nphoang1102/mqp-mech/C-term/Testing/test_top_part_Feb_18_2018_(FINISHED).SLDASM

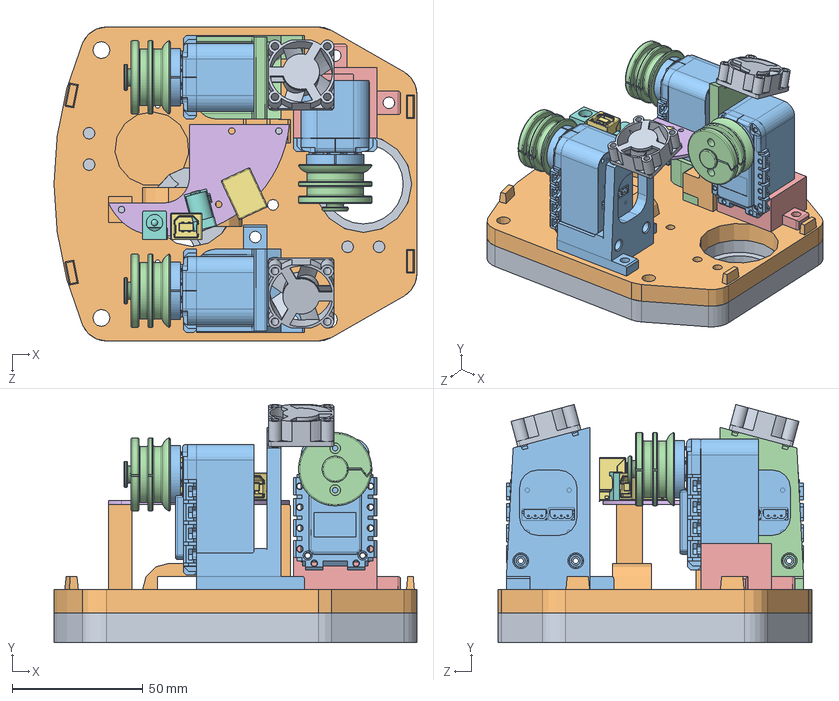
[picture p16: CAD file, 2018-03-26]
C-term/Testing/test_top_part_Feb_18_2018_(FINISHED).SLDASM
138.7 x 90.9 x 120.0 mm
base_prototype_bottom_(Feb_18_2018)
base_prototype_top_(Feb_18_2018)
mount_finger_left_(FAN_ADJUST)
mount_finger_right_(FAN_ADJUST)
mount_thumb_(MODIFIED_FOR_MOTOR)
Pcb board base
USB type b
power jack
DC Fan - 25X25X10 x 2
PCB_board_mount_standing
AX-12A (back off) x 3
pulley_spool_test x 3
