nphoang1102/mqp-mech/B-term/Prototype 1 Fixes (Not Prototype 2 Yet)/XL320_and_mount.SLDASM

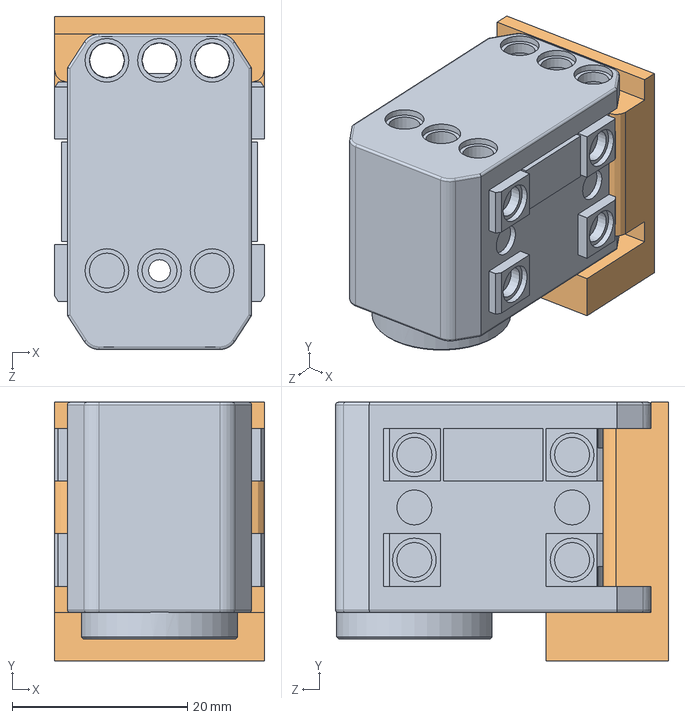
[picture p17: CAD file, 2018-03-26]
B-term/Prototype 1 Fixes (Not Prototype 2 Yet)/XL320_and_mount.SLDASM
24.0 x 29.5 x 38.0 mm
XL320
XL320_thumb_mount
