nphoang1102/mqp-mech/B-term/Prototype 1 Fixes (Not Prototype 2 Yet)/motor_pulley_thumb.SLDASM

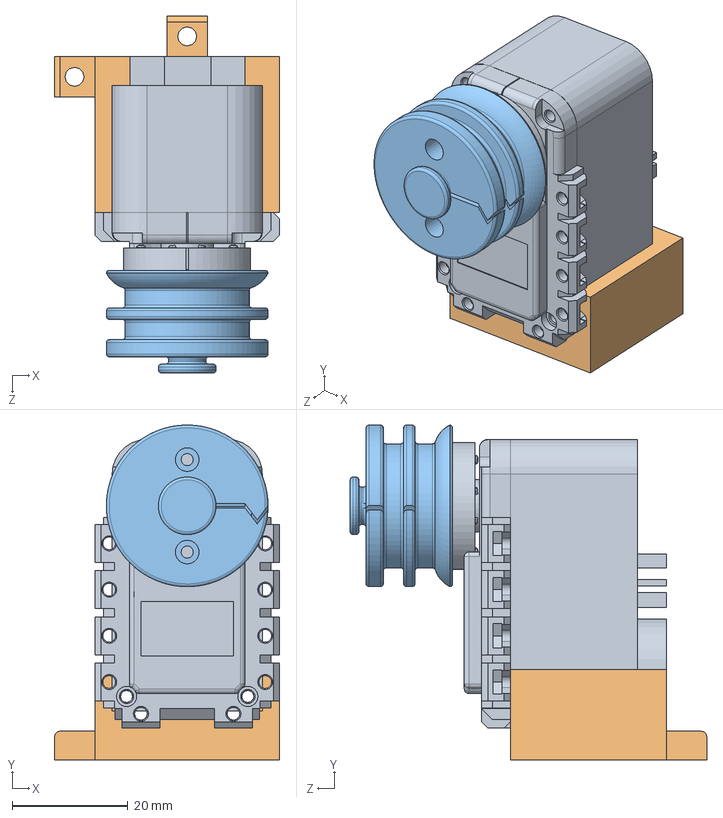
[picture p18: CAD file, 2018-03-26]
B-term/Prototype 1 Fixes (Not Prototype 2 Yet)/motor_pulley_thumb.SLDASM
39.0 x 58.0 x 61.7 mm
AX-12A (back off)
AX12_thumb_mount
pulley_spool_test
