nphoang1102/mqp-mech/B-term/Prototype 2/test_bottom_part_(FINISHED).SLDASM

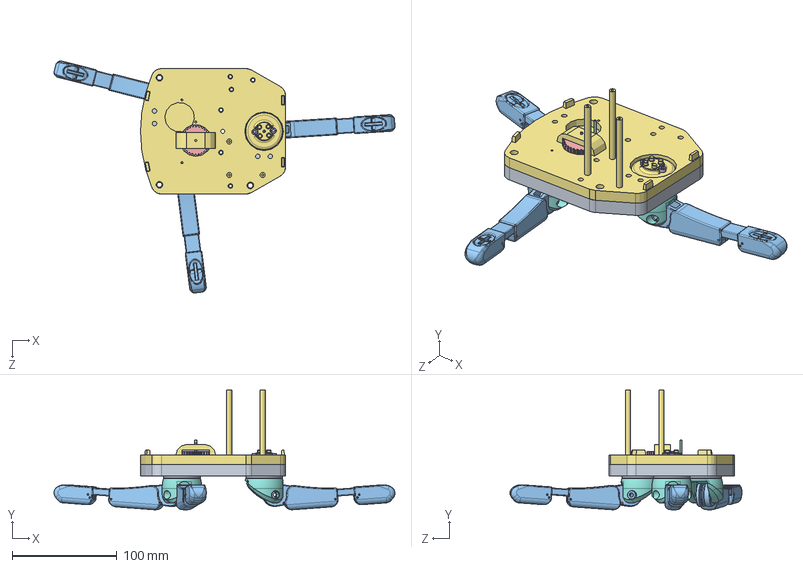
[picture p19: CAD file, 2018-03-26]
B-term/Prototype 2/test_bottom_part_(FINISHED).SLDASM
326.0 x 114.4 x 221.9 mm
base_prototype_bottom
gear_finger_left
gear_finger_right
gear_rod_(NOT_PRINT) x 2
gear_two_stage
gear_intermediate
mount_knuckle_test_modified
Knuckle mark 3 x 3
Delrin Washer x 3
M3 EZ LOCK (5.1MM HOLE) 6.5mm insert x 6
Finger x 3
M2_Washer_2.2mm_(TO_BUY)
M3_x_10mm_(TO_BUY) x 4
M3_x_22mm x 2
base_prototype_top
Hex_Nut_M4 x 6
Hex_Nut_M6 x 3
