nphoang1102/mqp-mech/A-term/motor_pulley_right.SLDASM

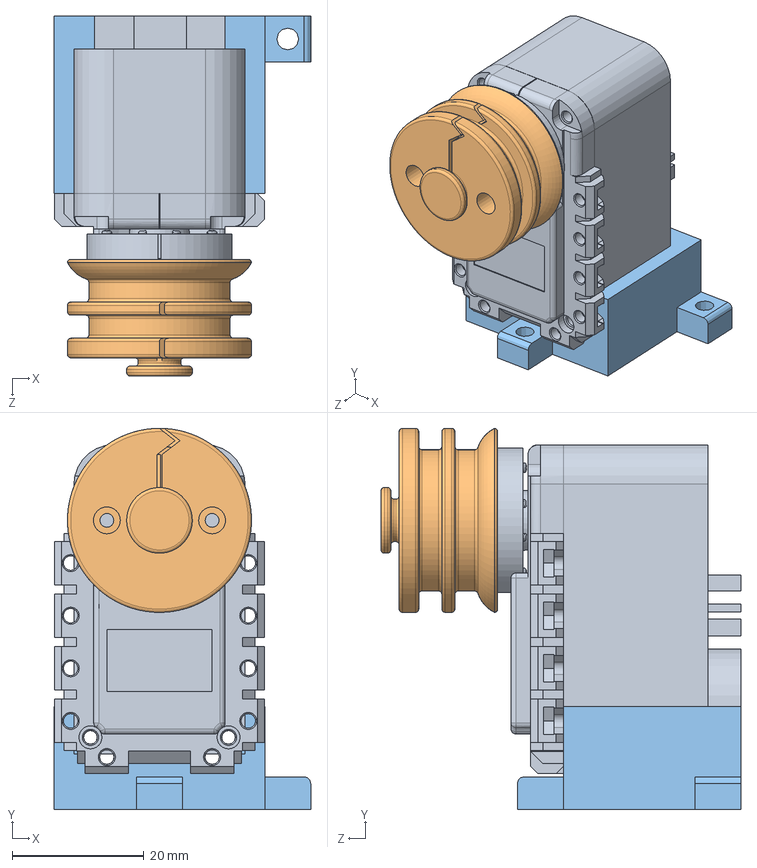
[picture p20: CAD file, 2017-10-21]
A-term/motor_pulley_right.SLDASM
39.0 x 58.0 x 54.8 mm
AX-12A (back off)
pulley_spool_test
AX12_front_mount_right
