nphoang1102/mqp-mech/B-term/Prototype 1 Fixes (Not Prototype 2 Yet)/TEST_POSITION_PROTOTYPE_2.SLDASM

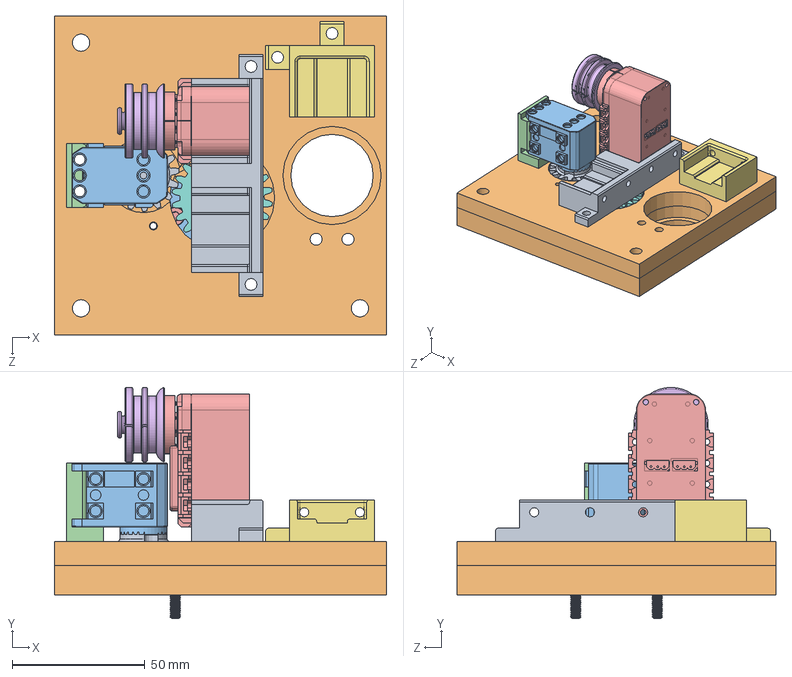
[picture p21: CAD file, 2018-03-26]
B-term/Prototype 1 Fixes (Not Prototype 2 Yet)/TEST_POSITION_PROTOTYPE_2.SLDASM
125.0 x 87.0 x 120.0 mm
two_stage_gear
drive_gear
base_prototype_test
finger_gear_left
finger_gear_right
91290A164_BLACK-OXIDE CLASS 12.9 SOCKET HEAD CAP SCREW x 2
gear_rod
