nphoang1102/mqp-mech/B-term/Prototype 2/test_top_part_with_shaft_(NOT_FINISHED).SLDASM

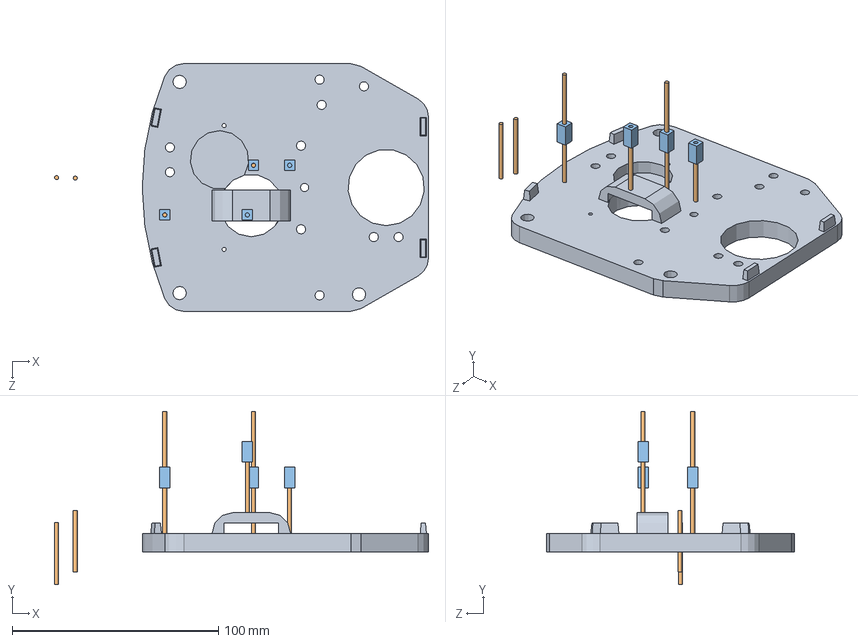
[picture p22: CAD file, 2018-03-26]
B-term/Prototype 2/test_top_part_with_shaft_(NOT_FINISHED).SLDASM
181.2 x 83.8 x 120.0 mm
base_prototype_top_(Jan_20_2018)
gear_rod_(NOT_PRINT) x 8
shaft_connector x 4
