nphoang1102/mqp-mech/B-term/Prototype 2/test_motor_pulley.SLDASM

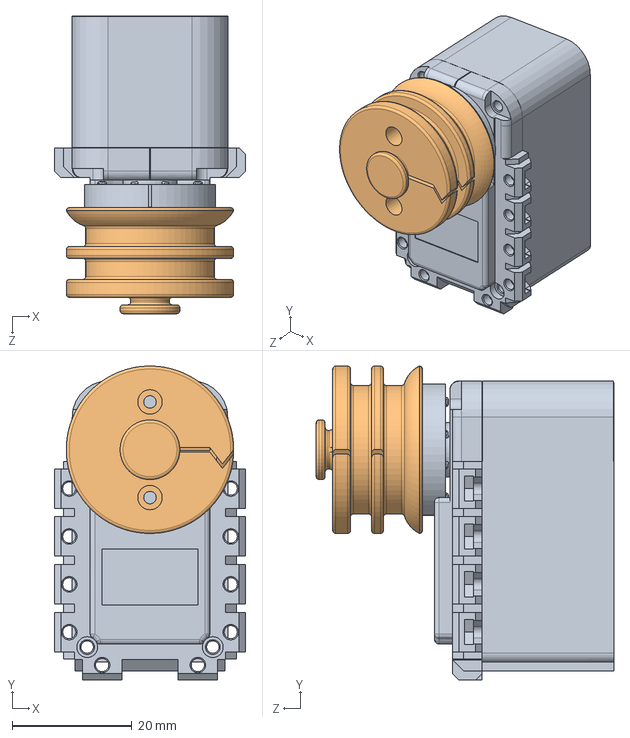
[picture p23: CAD file, 2018-03-26]
B-term/Prototype 2/test_motor_pulley.SLDASM
32.0 x 52.5 x 49.8 mm
AX-12A (back off)
pulley_spool_test
