nphoang1102/mqp-mech/A-term/motor_pulley_left.SLDASM

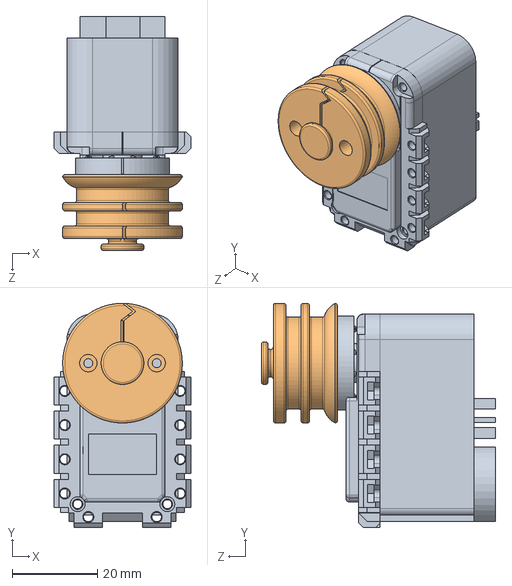
[picture p24: CAD file, 2017-10-21]
A-term/motor_pulley_left.SLDASM
32.0 x 52.5 x 54.8 mm
AX-12A (back off)
pulley_spool_test
