nphoang1102/mqp-mech/A-term/gears_train.SLDASM

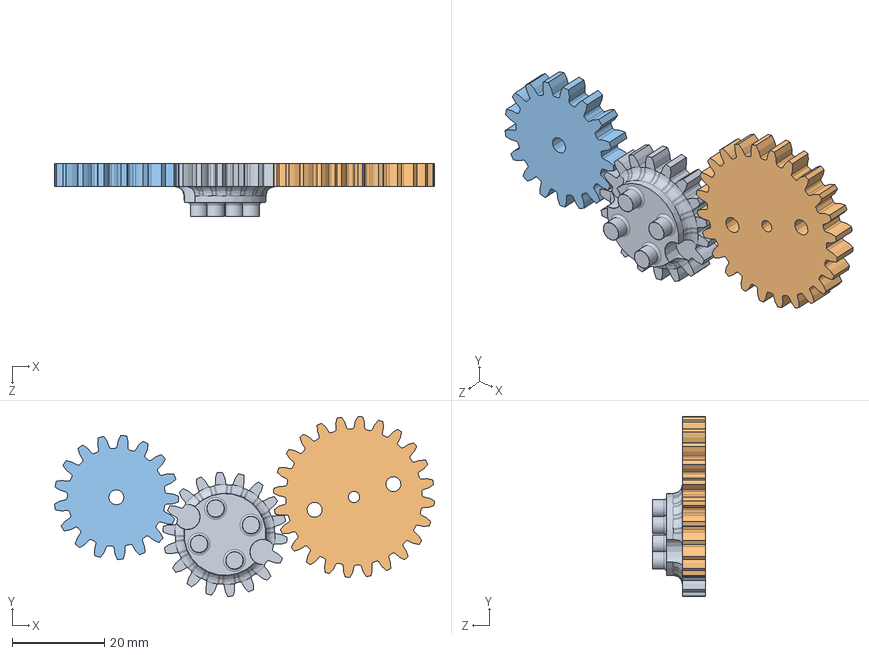
[picture p26: CAD file, 2017-10-08]
A-term/gears_train.SLDASM
82.5 x 39.1 x 11.5 mm
drive_gear
finger_gear
intermediate_gear
