nphoang1102/mqp-mech/A-term/positioning_motors_test.SLDASM

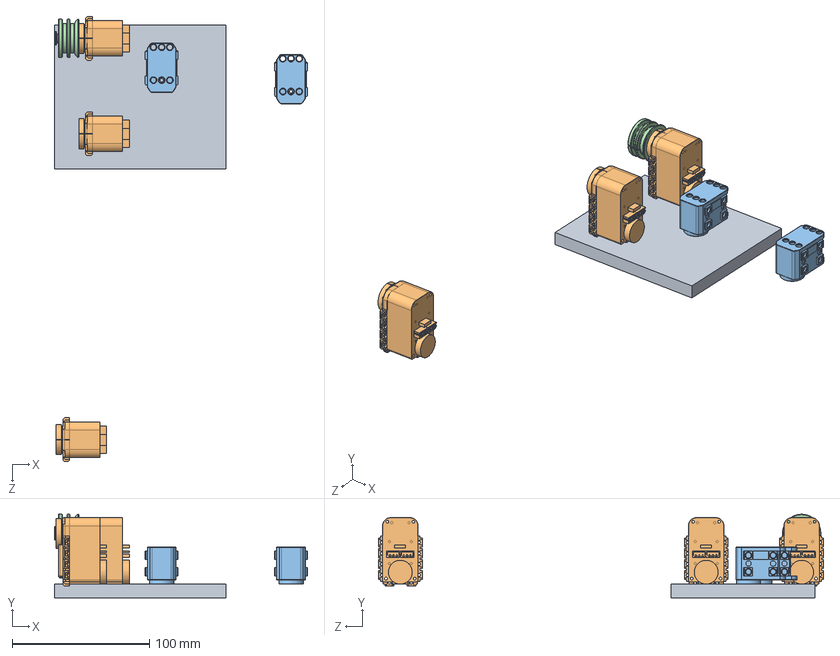
[picture p27: CAD file, 2017-10-04]
A-term/positioning_motors_test.SLDASM
184.6 x 61.0 x 324.8 mm
base_prototype_test
AX-12A (back off) x 3
XL320 x 2
pulley_spool_test
