nphoang1102/mqp-mech/B-term/Prototype 1 Fixes (Not Prototype 2 Yet)/finger_gear_right.SLDPRT

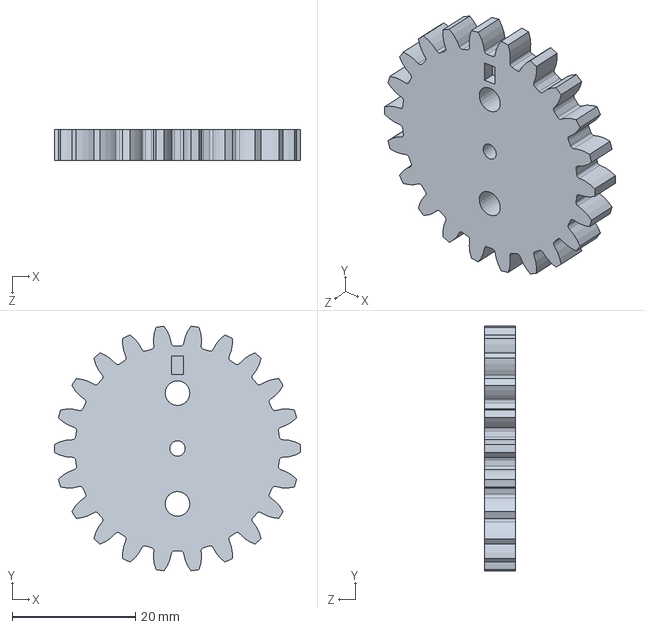
[picture p28: CAD file, 2018-03-26]
B-term/Prototype 1 Fixes (Not Prototype 2 Yet)/finger_gear_right.SLDPRT
40.0 x 39.8 x 5.00 mm
