nphoang1102/mqp-mech/B-term/Prototype 2/mount_board_(NOT_FINISHED).SLDPRT

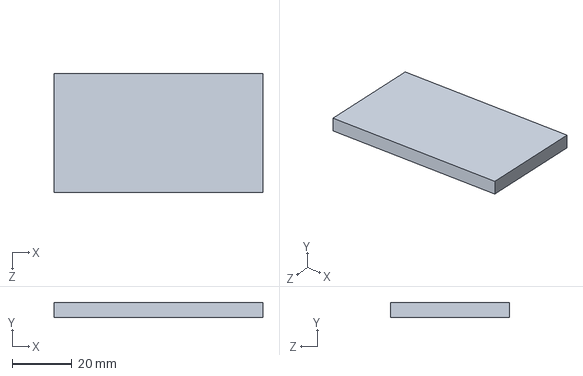
[picture p29: CAD file, 2018-03-26]
B-term/Prototype 2/mount_board_(NOT_FINISHED).SLDPRT
70.0 x 5.00 x 40.0 mm
