nphoang1102/mqp-mech/B-term/Prototype 2/STL/base_prototype_bottom_(Jan_10_2018).STL

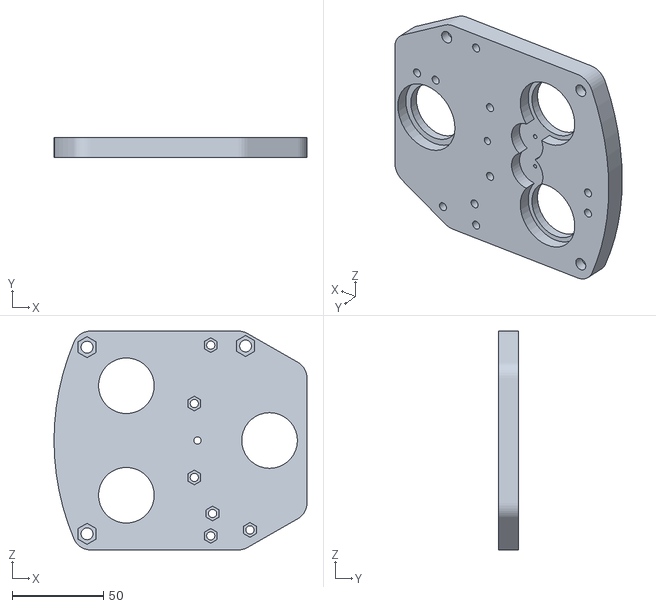
[picture p30: CAD file, 2018-03-26]
B-term/Prototype 2/STL/base_prototype_bottom_(Jan_10_2018).STL
138.7 x 11.2 x 120.0
