nphoang1102/mqp-mech/B-term/ReflexOne Finger/Knuckle mark 3.SLDPRT

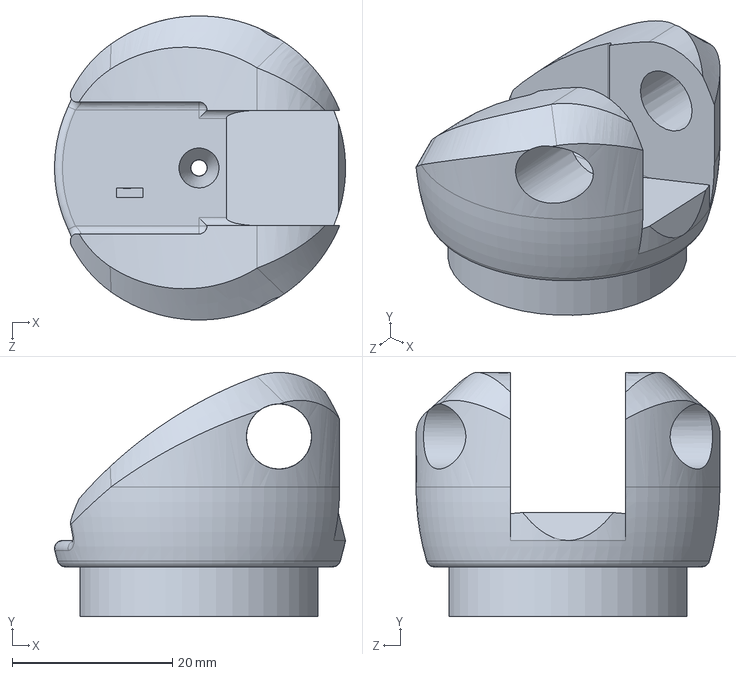
[picture p31: CAD file, 2018-03-26]
B-term/ReflexOne Finger/Knuckle mark 3.SLDPRT
36.4 x 30.5 x 38.0 mm
