nphoang1102/mqp-mech/C-term/Modified Parts/mount_finger_left.SLDPRT

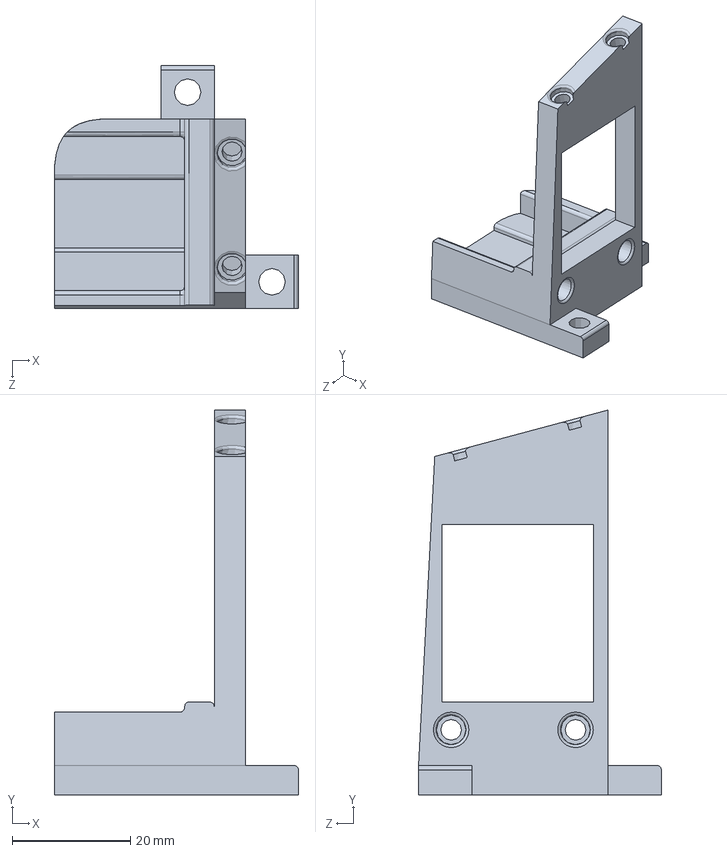
[picture p32: CAD file, 2018-03-26]
C-term/Modified Parts/mount_finger_left.SLDPRT
41.2 x 65.0 x 41.0 mm
