nphoang1102/mqp-mech/C-term/Mounting Parts/camera_adapter_base_modified.SLDPRT

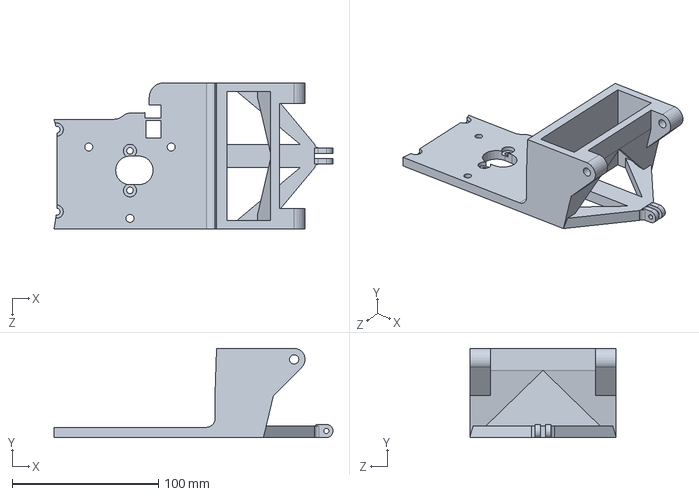
[picture p33: CAD file, 2018-03-26]
C-term/Mounting Parts/camera_adapter_base_modified.SLDPRT
190.5 x 60.9 x 100.0 mm
