nphoang1102/mqp-mech/C-term/STL toPrint/Feb_11_2018/base_prototype_top_(Feb_9_2018).STL

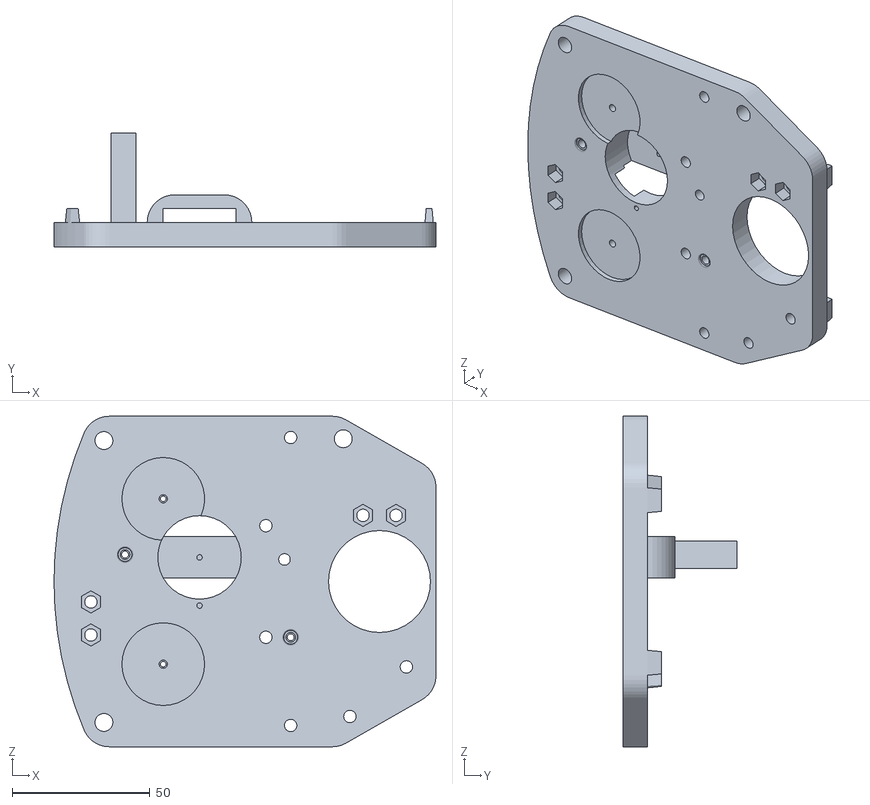
[picture p34: CAD file, 2018-03-26]
C-term/STL toPrint/Feb_11_2018/base_prototype_top_(Feb_9_2018).STL
138.7 x 41.5 x 120.0
