nphoang1102/mqp-mech/C-term/STL toPrint/Feb_13_2018/glove_housing_top.STL

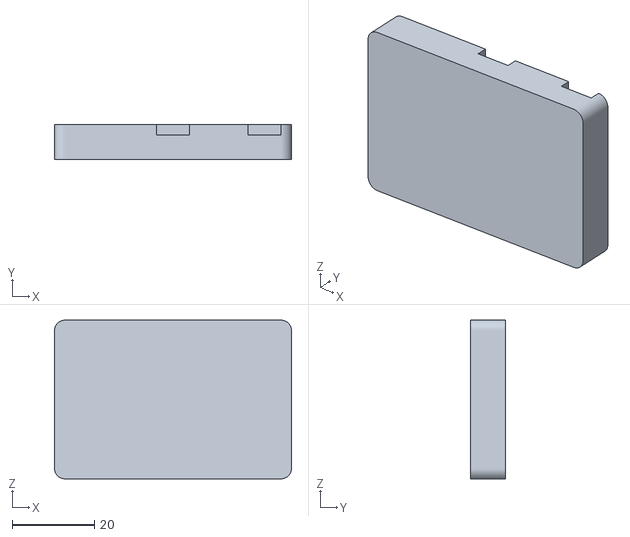
[picture p35: CAD file, 2018-03-26]
C-term/STL toPrint/Feb_13_2018/glove_housing_top.STL
57.5 x 8.50 x 38.5
