nphoang1102/mqp-mech/C-term/STL toPrint/Feb_25_2018/housing.STL

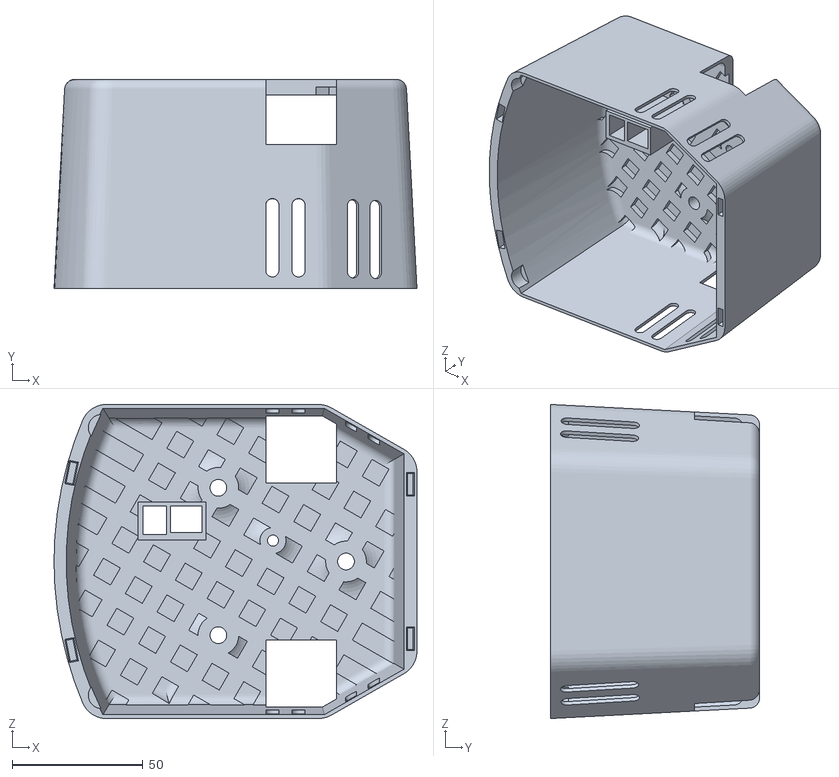
[picture p37: CAD file, 2018-03-26]
C-term/STL toPrint/Feb_25_2018/housing.STL
138.7 x 80.0 x 120.0
