nphoang1102/mqp-mech/C-term/STL toPrint/Feb_28_2018_RapidPrototyping/gear_two_stage.STL

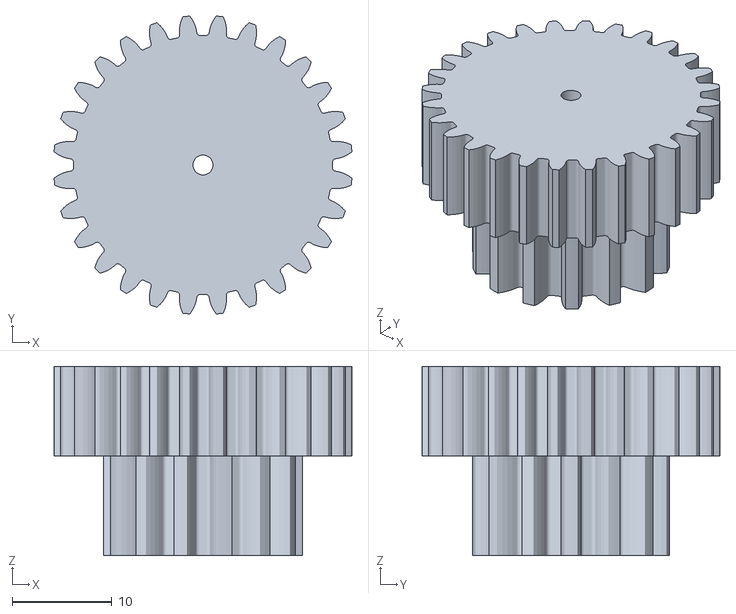
[picture p39: CAD file, 2018-03-26]
C-term/STL toPrint/Feb_28_2018_RapidPrototyping/gear_two_stage.STL
29.9 x 29.9 x 19.0
