nphoang1102/mqp-mech/C-term/STL toPrint/March_22_2018/mount_finger_right_(FAN_ADJUST).STL

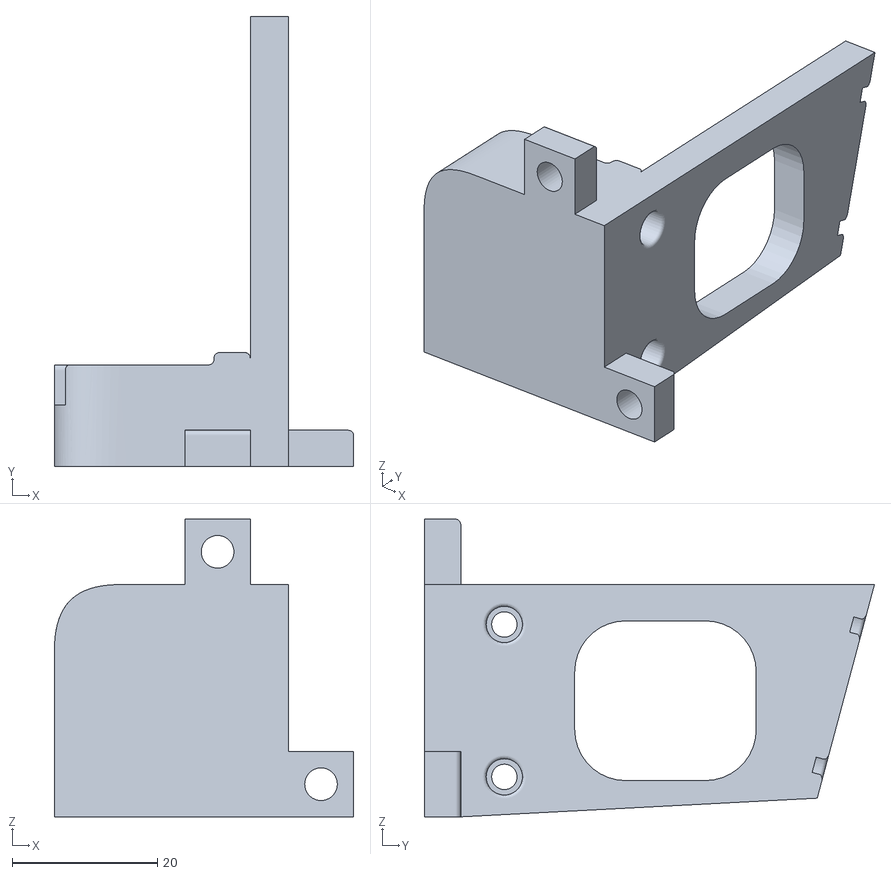
[picture p40: CAD file, 2018-03-26]
C-term/STL toPrint/March_22_2018/mount_finger_right_(FAN_ADJUST).STL
41.2 x 62.0 x 41.0
