nphoang1102/mqp-mech/A-term/base_prototype_test.SLDPRT

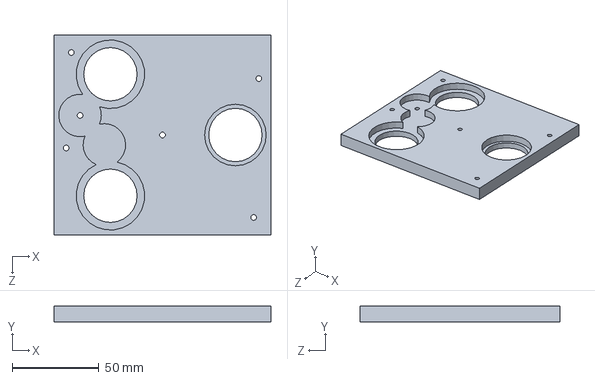
[picture p41: CAD file, 2017-10-24]
A-term/base_prototype_test.SLDPRT
125.0 x 9.22 x 115.0 mm
