nphoang1102/mqp-mech/B-term/Prototype 1 Fixes (Not Prototype 2 Yet)/gear_rod.SLDPRT

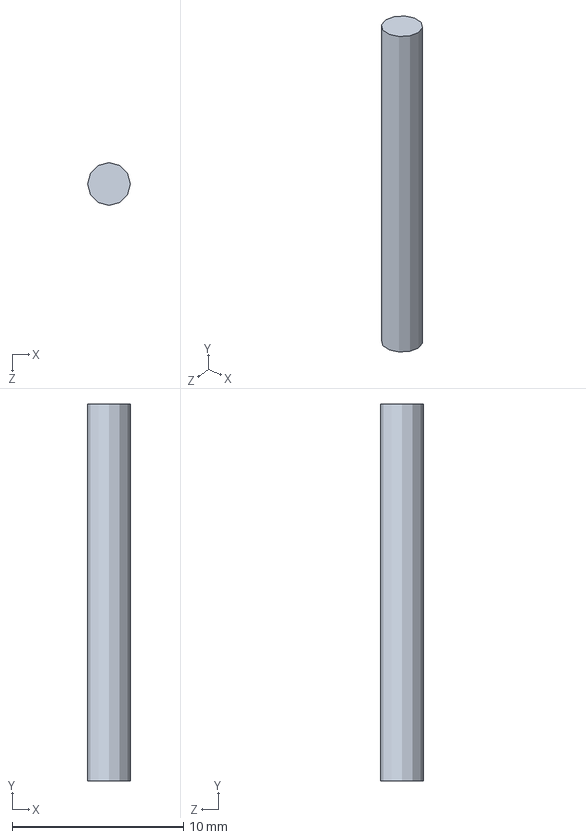
[picture p42: CAD file, 2018-03-26]
B-term/Prototype 1 Fixes (Not Prototype 2 Yet)/gear_rod.SLDPRT
2.50 x 22.0 x 2.50 mm
