nphoang1102/mqp-mech/B-term/Prototype 2/pulley_spool_test.SLDPRT

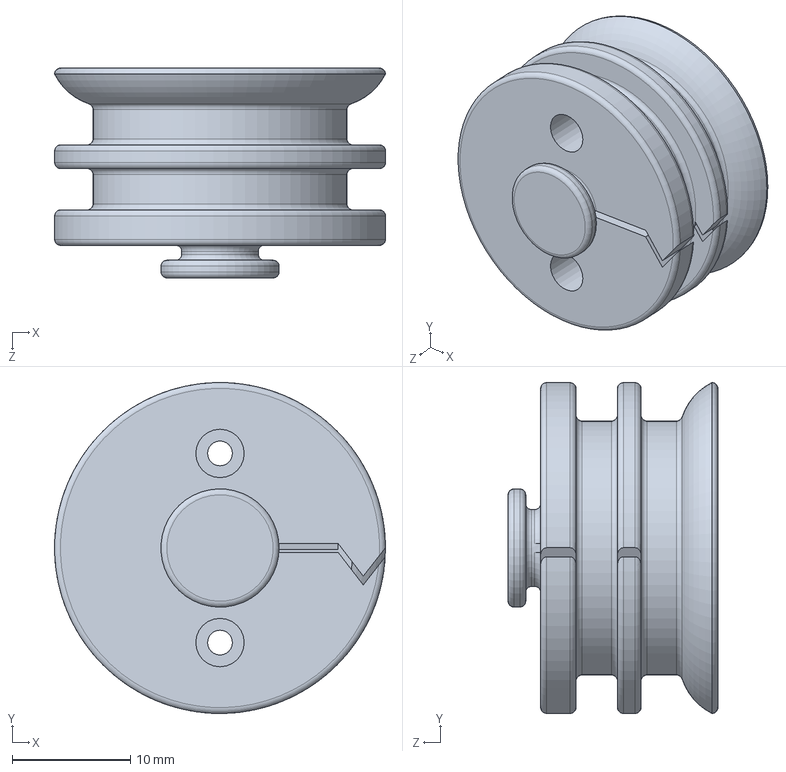
[picture p43: CAD file, 2018-03-26]
B-term/Prototype 2/pulley_spool_test.SLDPRT
28.0 x 28.0 x 17.8 mm
