nphoang1102/mqp-mech/B-term/Prototype 2/STL/housing.STL

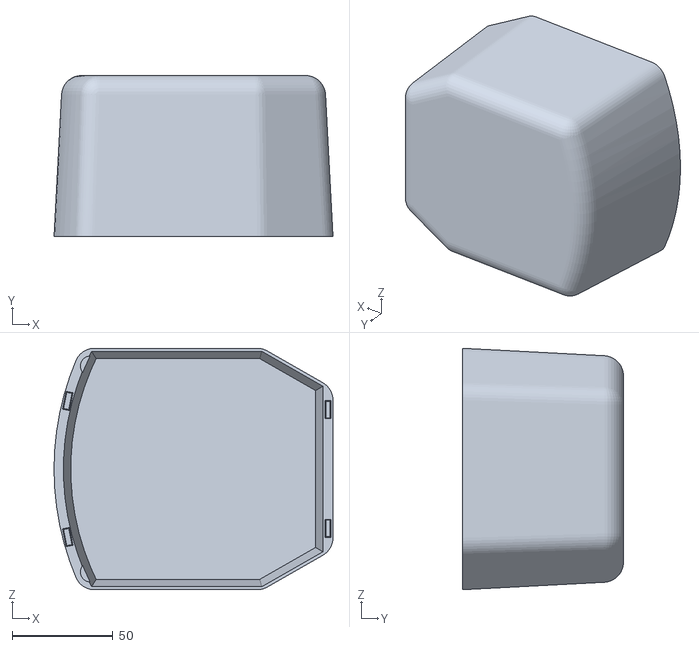
[picture p44: CAD file, 2018-03-26]
B-term/Prototype 2/STL/housing.STL
138.7 x 80.0 x 120.0
