nphoang1102/mqp-mech/C-term/Modified Parts/housing_(FINISHED).SLDPRT

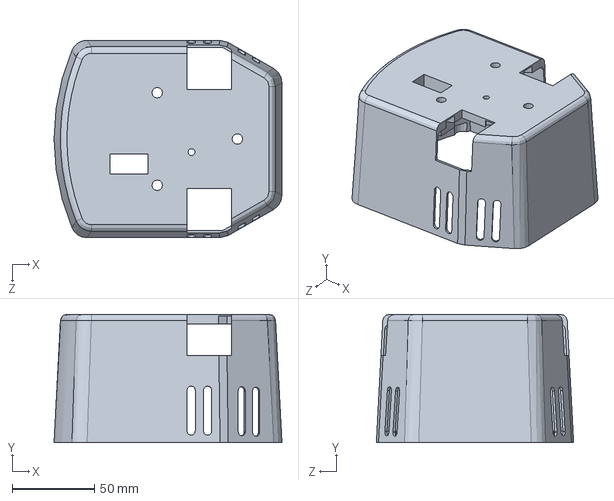
[picture p45: CAD file, 2018-03-26]
C-term/Modified Parts/housing_(FINISHED).SLDPRT
138.7 x 78.0 x 120.0 mm
