nphoang1102/mqp-mech/C-term/Mounting Parts/mounting_house/Camera Mount/ReflexHand_Camera_Adaptor_v2.SLDPRT

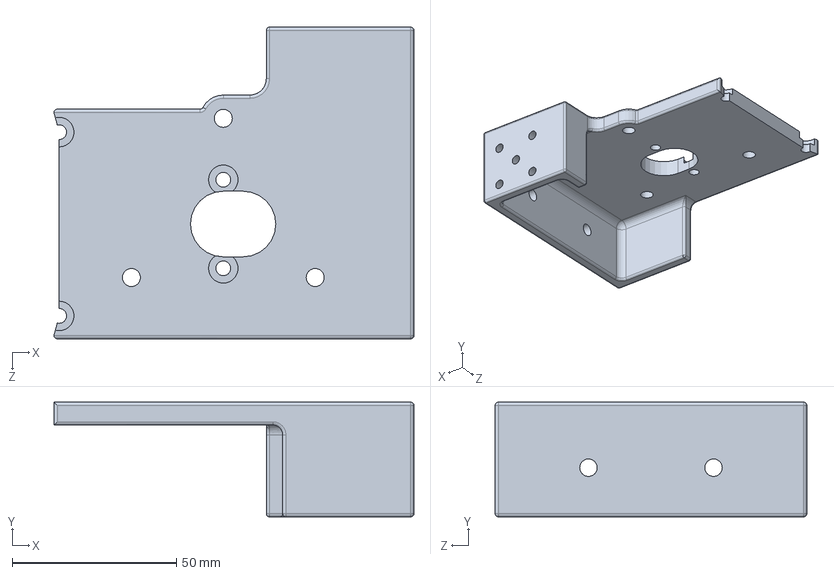
[picture p46: CAD file, 2018-03-26]
C-term/Mounting Parts/mounting_house/Camera Mount/ReflexHand_Camera_Adaptor_v2.SLDPRT
109.7 x 35.0 x 95.0 mm
