nphoang1102/mqp-mech/C-term/Mounting Parts/test_shape_fan_mount.SLDPRT

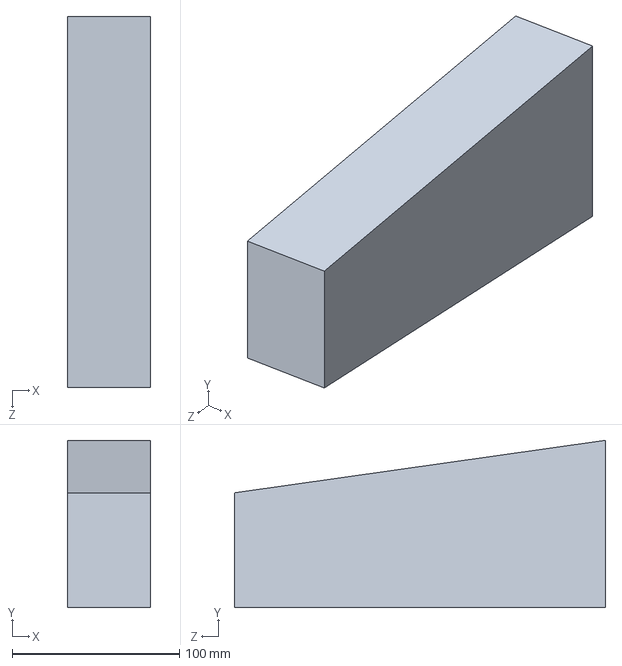
[picture p47: CAD file, 2018-03-26]
C-term/Mounting Parts/test_shape_fan_mount.SLDPRT
49.6 x 100.0 x 221.7 mm
