nphoang1102/mqp-mech/C-term/PCB Mount/USB type b.SLDPRT

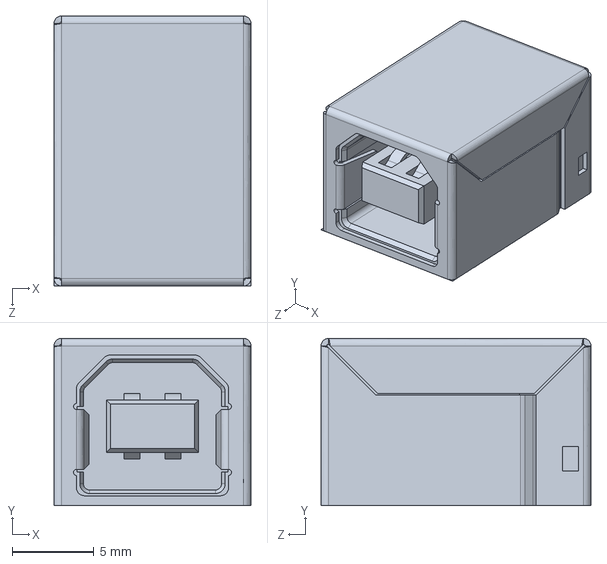
[picture p48: CAD file, 2018-03-26]
C-term/PCB Mount/USB type b.SLDPRT
12.0 x 10.2 x 16.5 mm
