nphoang1102/mqp-mech/C-term/STL toPrint/Feb_11_2018/mount_thumb.STL

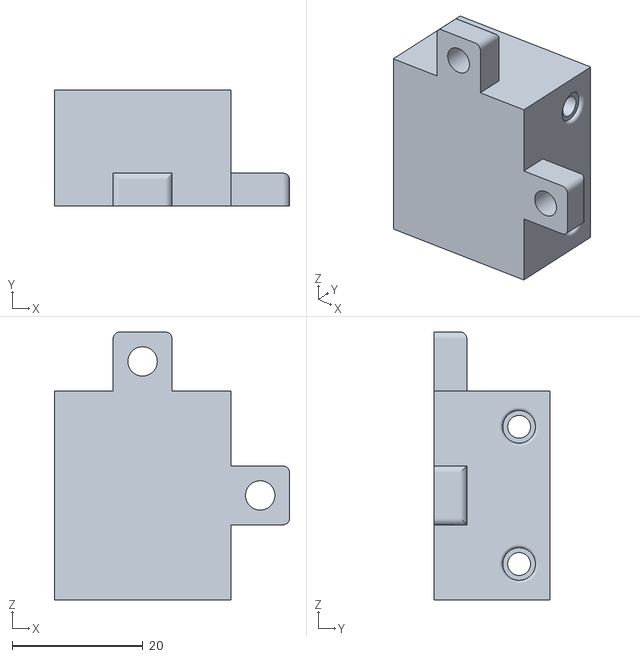
[picture p49: CAD file, 2018-03-26]
C-term/STL toPrint/Feb_11_2018/mount_thumb.STL
36.0 x 17.7 x 41.0
