nphoang1102/mqp-mech/C-term/STL toPrint/Feb_13_2018/glove_housing_bottom.STL

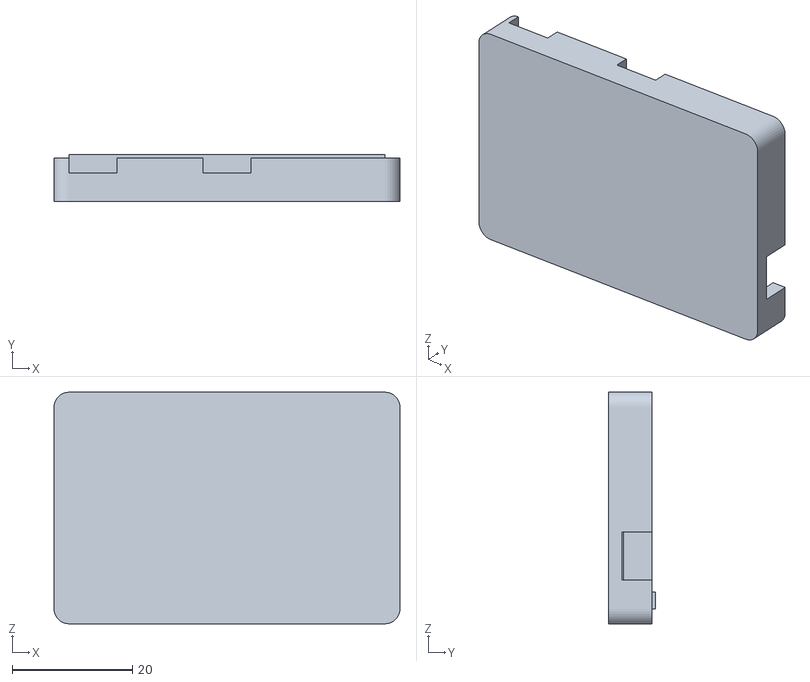
[picture p50: CAD file, 2018-03-26]
C-term/STL toPrint/Feb_13_2018/glove_housing_bottom.STL
57.5 x 7.85 x 38.5
