nphoang1102/mqp-mech/C-term/STL toPrint/Feb_28_2018_RapidPrototyping/mount_XL320_drive.STL

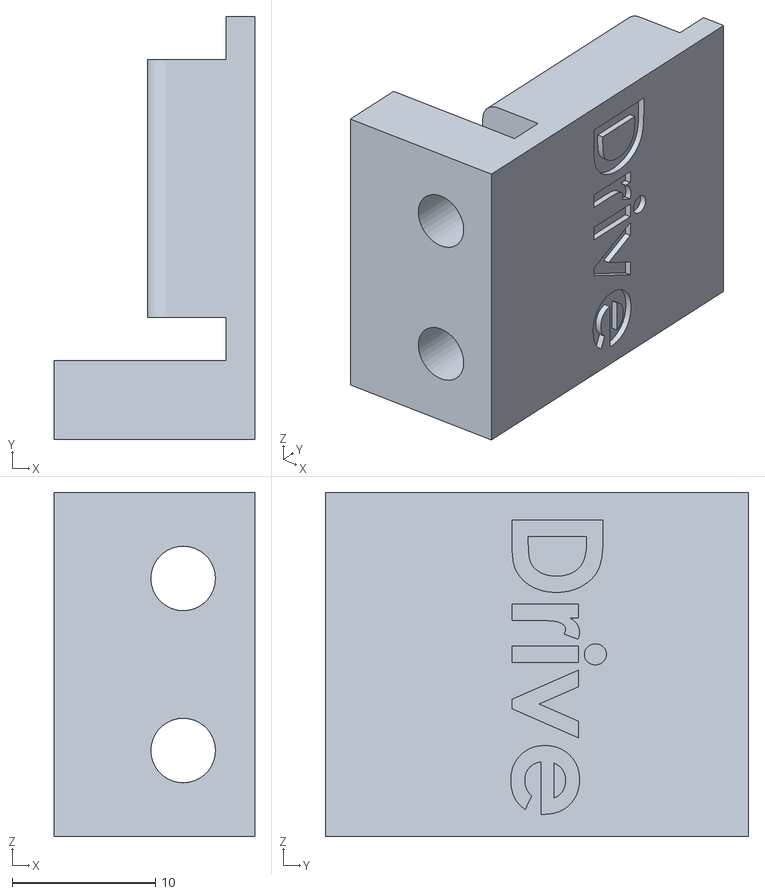
[picture p53: CAD file, 2018-03-26]
C-term/STL toPrint/Feb_28_2018_RapidPrototyping/mount_XL320_drive.STL
14.0 x 29.5 x 24.0
