nphoang1102/mqp-mech/C-term/STL toPrint/Jan_29_2018/gear_finger.STL

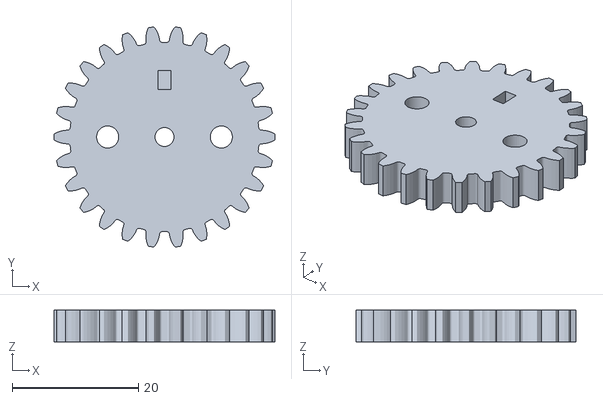
[picture p54: CAD file, 2018-03-26]
C-term/STL toPrint/Jan_29_2018/gear_finger.STL
35.0 x 34.8 x 5.00
