nphoang1102/mqp-mech/A-term/connect_shaft.SLDPRT

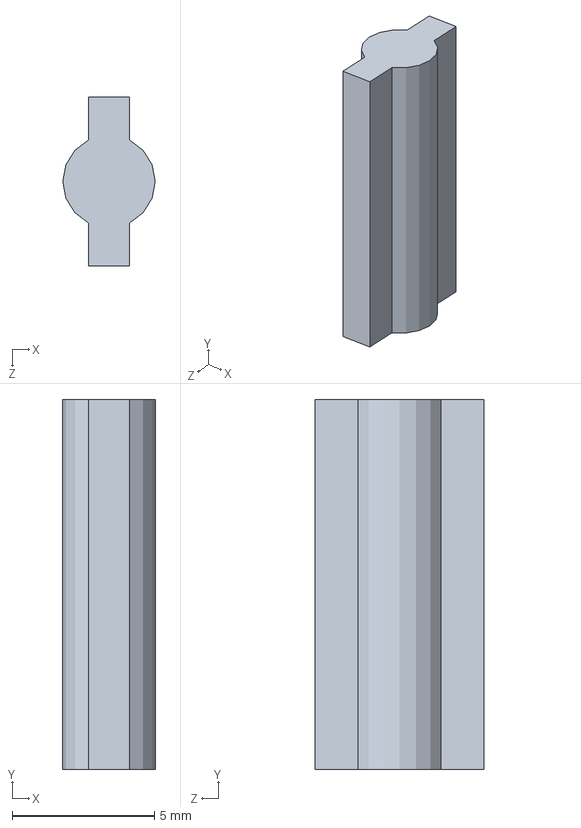
[picture p55: CAD file, 2017-10-24]
A-term/connect_shaft.SLDPRT
3.25 x 13.0 x 5.95 mm
