nphoang1102/mqp-mech/B-term/Prototype 1 Fixes (Not Prototype 2 Yet)/drive_gear.SLDPRT

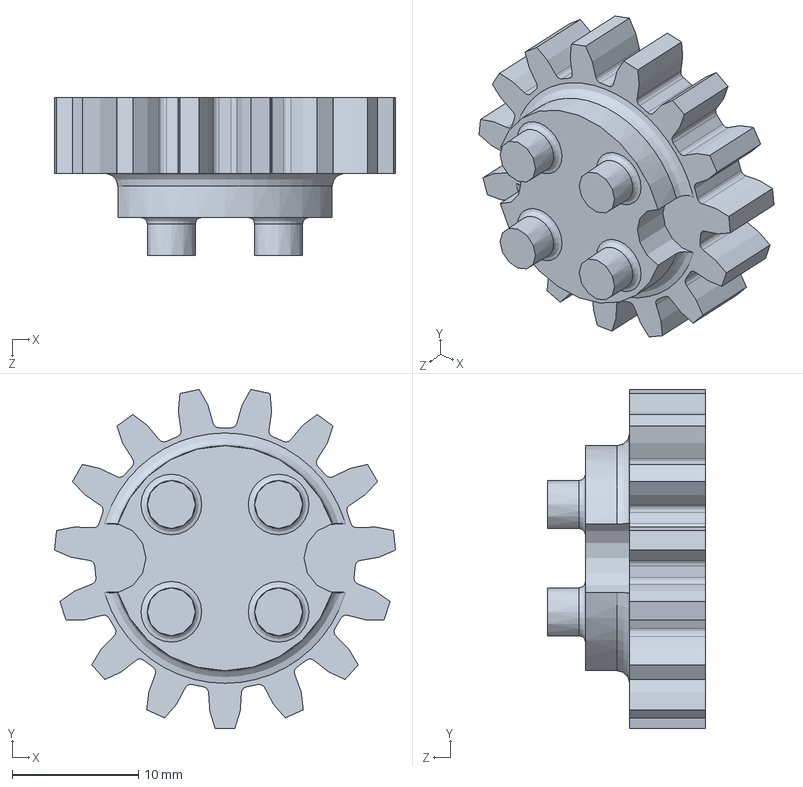
[picture p56: CAD file, 2018-03-26]
B-term/Prototype 1 Fixes (Not Prototype 2 Yet)/drive_gear.SLDPRT
27.0 x 26.8 x 12.5 mm
