nphoang1102/mqp-mech/B-term/Prototype 2/STL/base_prototype_top_(Jan_20_2018).STL

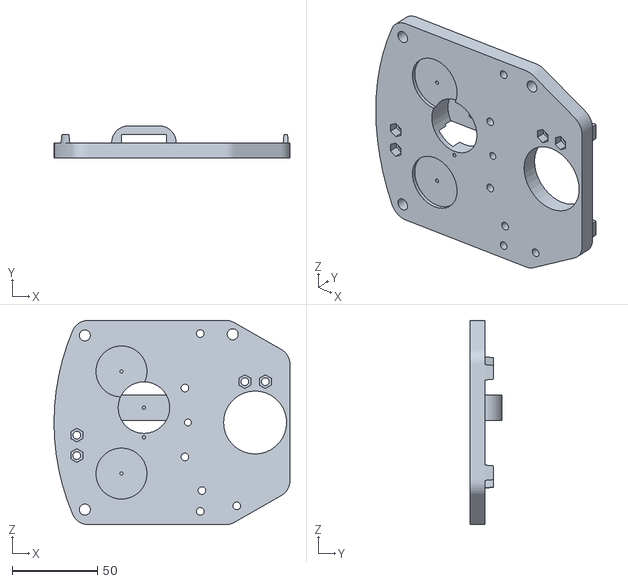
[picture p57: CAD file, 2018-03-26]
B-term/Prototype 2/STL/base_prototype_top_(Jan_20_2018).STL
138.7 x 19.0 x 120.0
