nphoang1102/mqp-mech/C-term/PCB Mount/Molex Picoblade 2pin (for Sunon DC Fan).SLDPRT

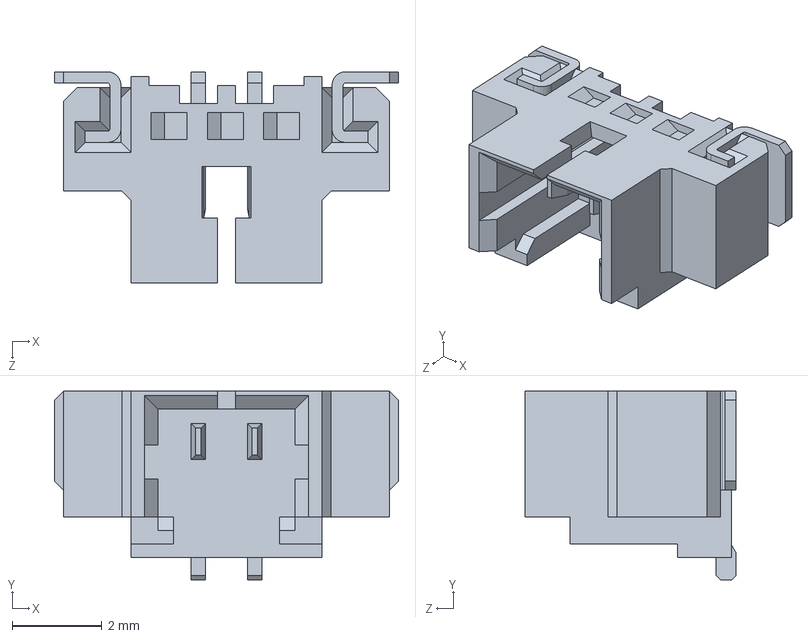
[picture p58: CAD file, 2018-03-26]
C-term/PCB Mount/Molex Picoblade 2pin (for Sunon DC Fan).SLDPRT
7.65 x 4.20 x 4.70 mm
