nphoang1102/mqp-mech/C-term/STL toPrint/Feb_11_2018/PCB_board_mount_standing.STL

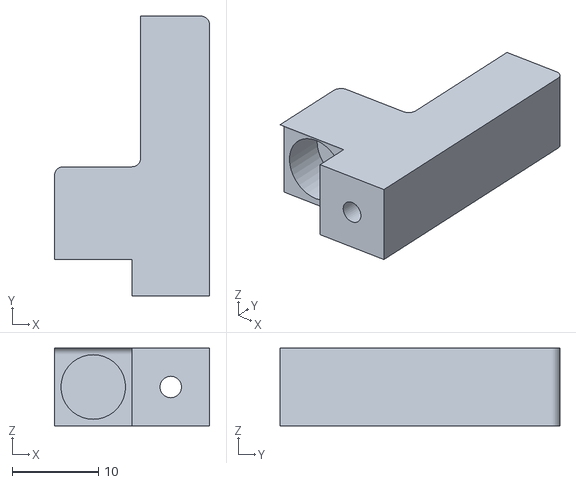
[picture p59: CAD file, 2018-03-26]
C-term/STL toPrint/Feb_11_2018/PCB_board_mount_standing.STL
18.0 x 32.5 x 9.00
