nphoang1102/mqp-mech/C-term/STL toPrint/March_16_2018/glove_housing_bottom.STL

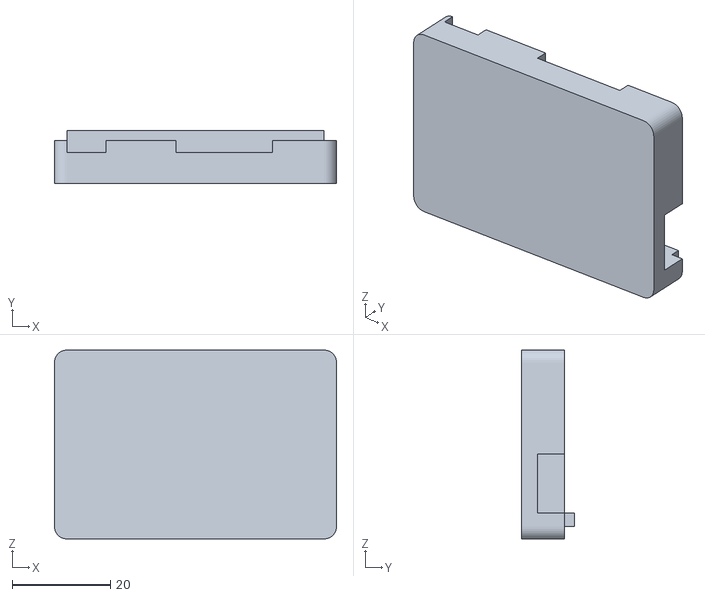
[picture p60: CAD file, 2018-03-26]
C-term/STL toPrint/March_16_2018/glove_housing_bottom.STL
57.5 x 10.8 x 38.5
