nphoang1102/mqp-mech/A-term/top_part_base_prototype.SLDPRT

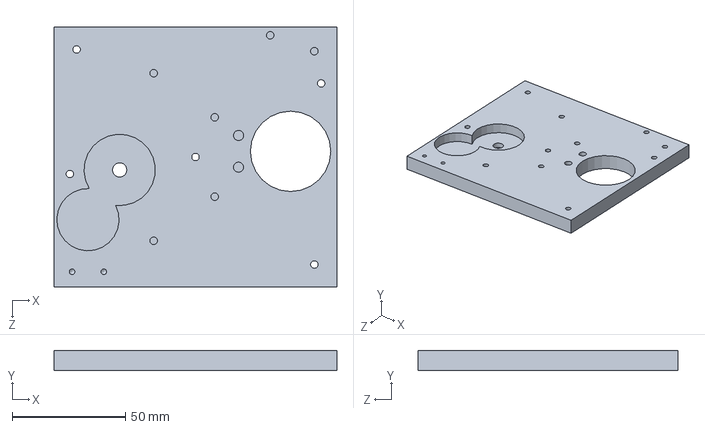
[picture p61: CAD file, 2017-10-24]
A-term/top_part_base_prototype.SLDPRT
125.0 x 9.00 x 115.0 mm
