nphoang1102/mqp-mech/B-term/Prototype 1 Fixes (Not Prototype 2 Yet)/AX12_fingers_mount (before modified to fit two-stage gear).SLDPRT

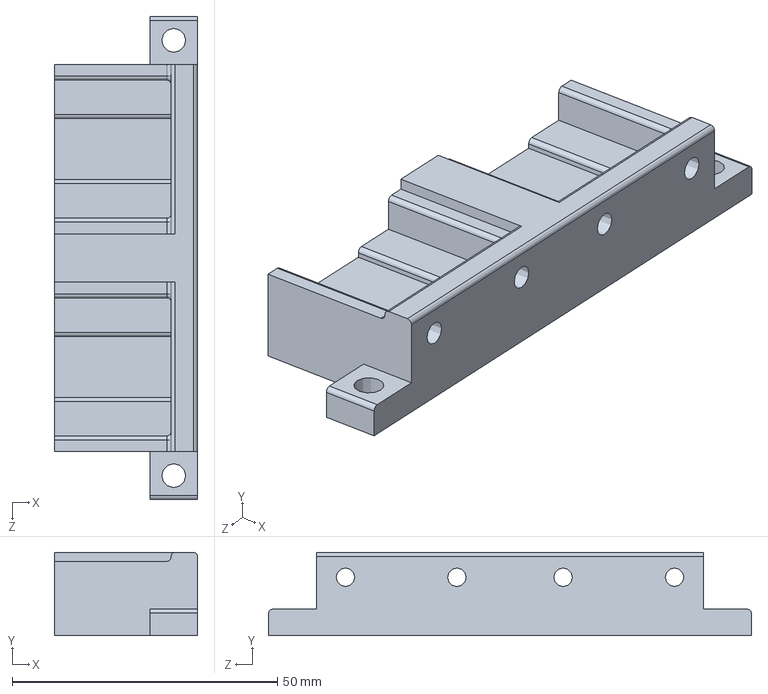
[picture p62: CAD file, 2018-03-26]
B-term/Prototype 1 Fixes (Not Prototype 2 Yet)/AX12_fingers_mount (before modified to fit two-stage gear).SLDPRT
27.0 x 15.7 x 91.0 mm
