nphoang1102/mqp-mech/B-term/Prototype 2/gear_rod_(NOT_PRINT).SLDPRT

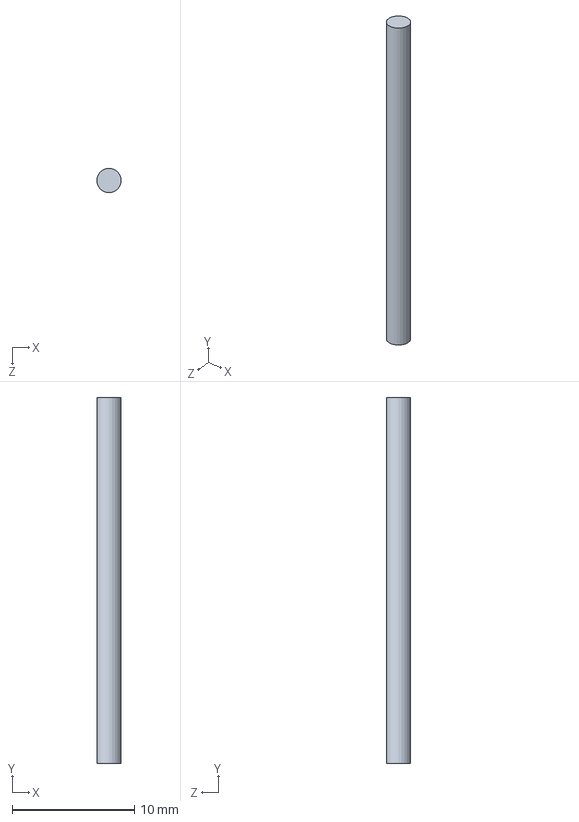
[picture p63: CAD file, 2018-03-26]
B-term/Prototype 2/gear_rod_(NOT_PRINT).SLDPRT
2.00 x 30.0 x 2.00 mm
