nphoang1102/mqp-mech/B-term/ReflexOne Finger/M3 EZ LOCK (5.1MM HOLE) 6.5mm insert.SLDPRT

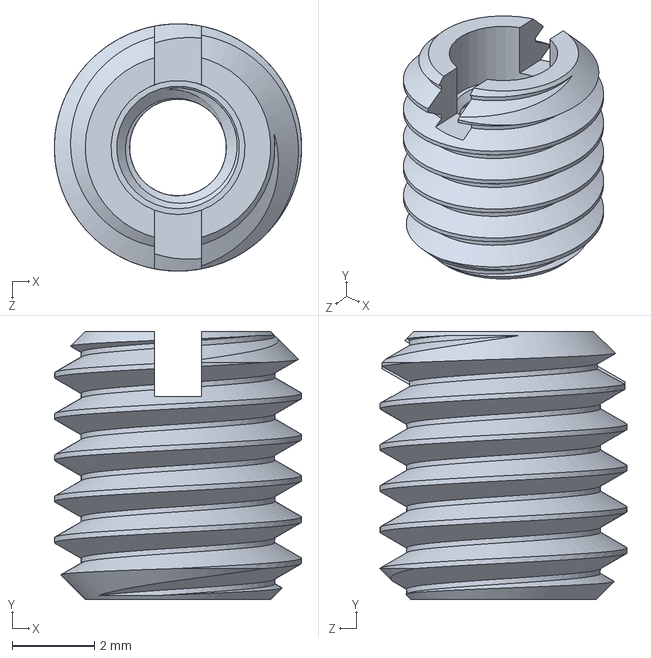
[picture p64: CAD file, 2017-10-08]
B-term/ReflexOne Finger/M3 EZ LOCK (5.1MM HOLE) 6.5mm insert.SLDPRT
6.00 x 6.50 x 6.00 mm
