nphoang1102/mqp-mech/C-term/Modified Parts/housing_(USED_FOR_REFERENCE).SLDPRT

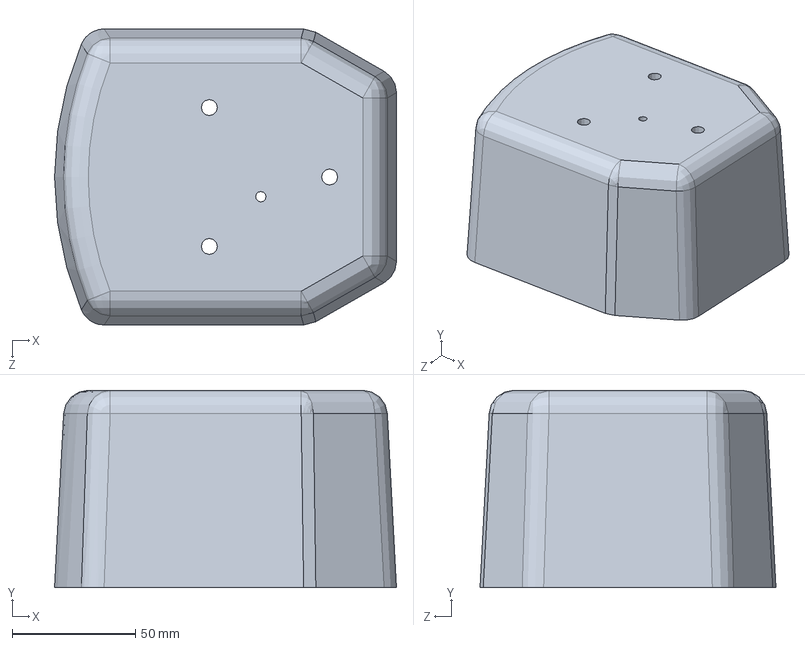
[picture p65: CAD file, 2018-03-26]
C-term/Modified Parts/housing_(USED_FOR_REFERENCE).SLDPRT
138.7 x 80.0 x 120.0 mm
