nphoang1102/mqp-mech/C-term/Mounting Parts/mounting_house/Camera Mount/WristCameraMount_Spacer.SLDPRT

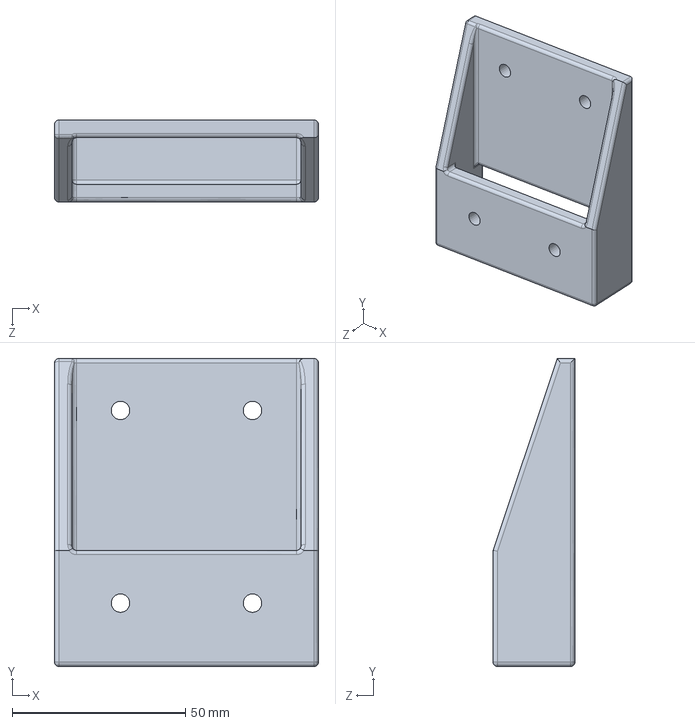
[picture p66: CAD file, 2018-03-26]
C-term/Mounting Parts/mounting_house/Camera Mount/WristCameraMount_Spacer.SLDPRT
76.2 x 88.9 x 23.6 mm
