nphoang1102/mqp-mech/C-term/PCB Mount/xl-320 connector.SLDPRT

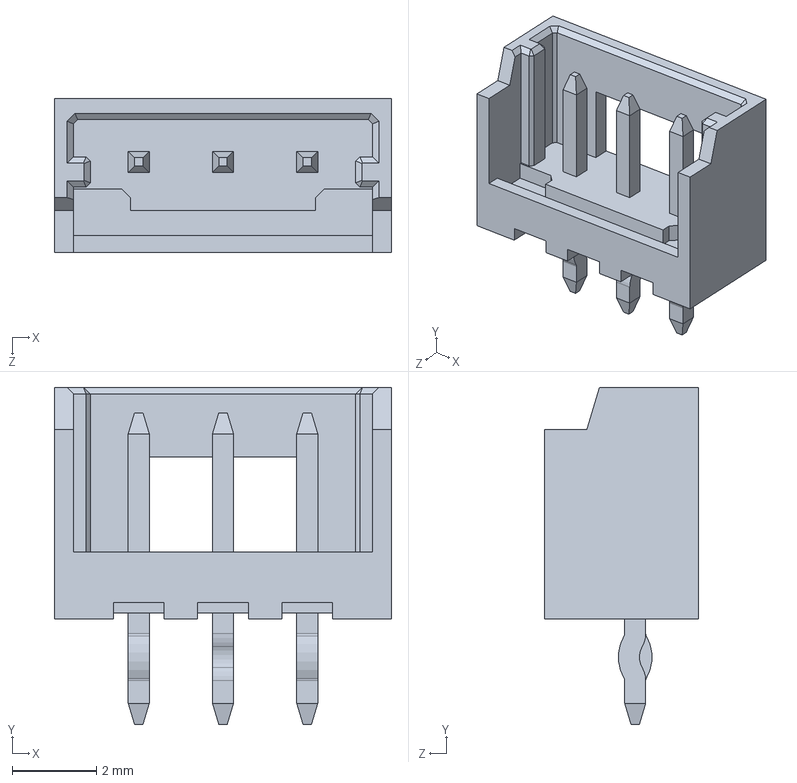
[picture p67: CAD file, 2018-03-26]
C-term/PCB Mount/xl-320 connector.SLDPRT
8.00 x 8.00 x 3.65 mm
