nphoang1102/mqp-mech/C-term/STL toPrint/Feb_18_2018/glove_housing_bottom.STL

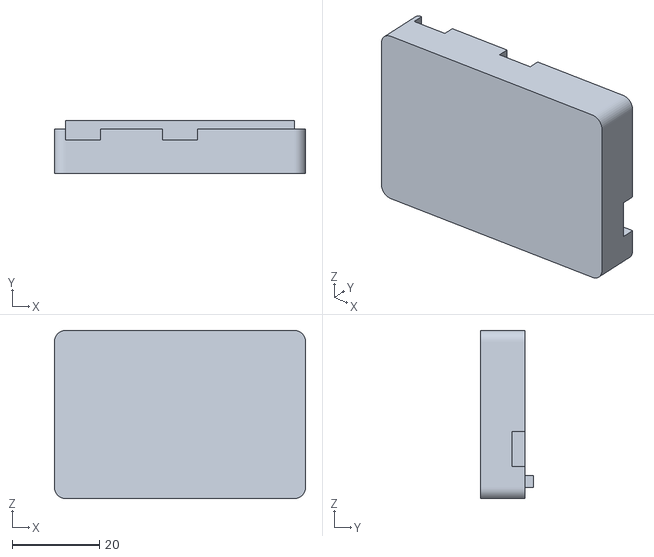
[picture p69: CAD file, 2018-03-26]
C-term/STL toPrint/Feb_18_2018/glove_housing_bottom.STL
57.5 x 12.2 x 38.5
