nphoang1102/mqp-mech/B-term/Prototype 2/gear_intermediate.SLDPRT

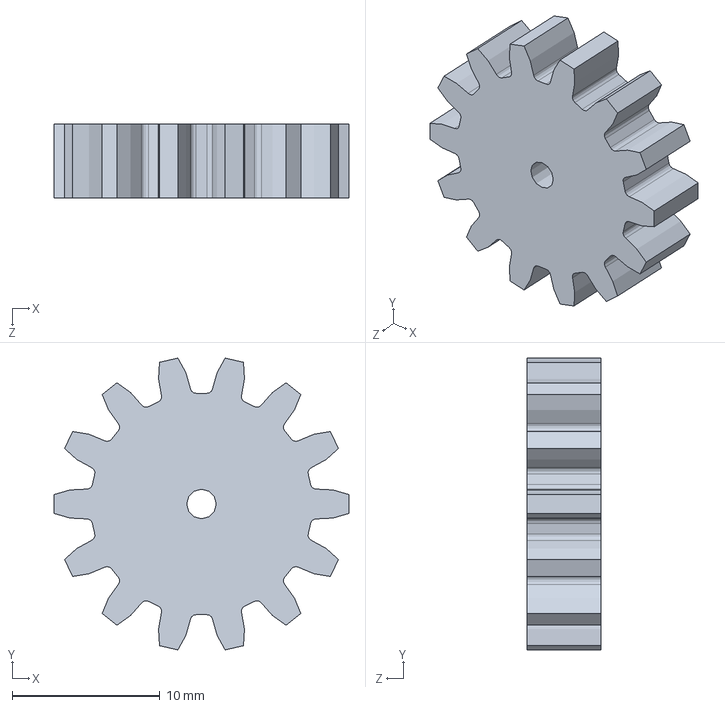
[picture p70: CAD file, 2018-03-26]
B-term/Prototype 2/gear_intermediate.SLDPRT
20.0 x 19.7 x 5.00 mm
