nphoang1102/mqp-mech/B-term/ReflexOne Finger/Finger.SLDPRT

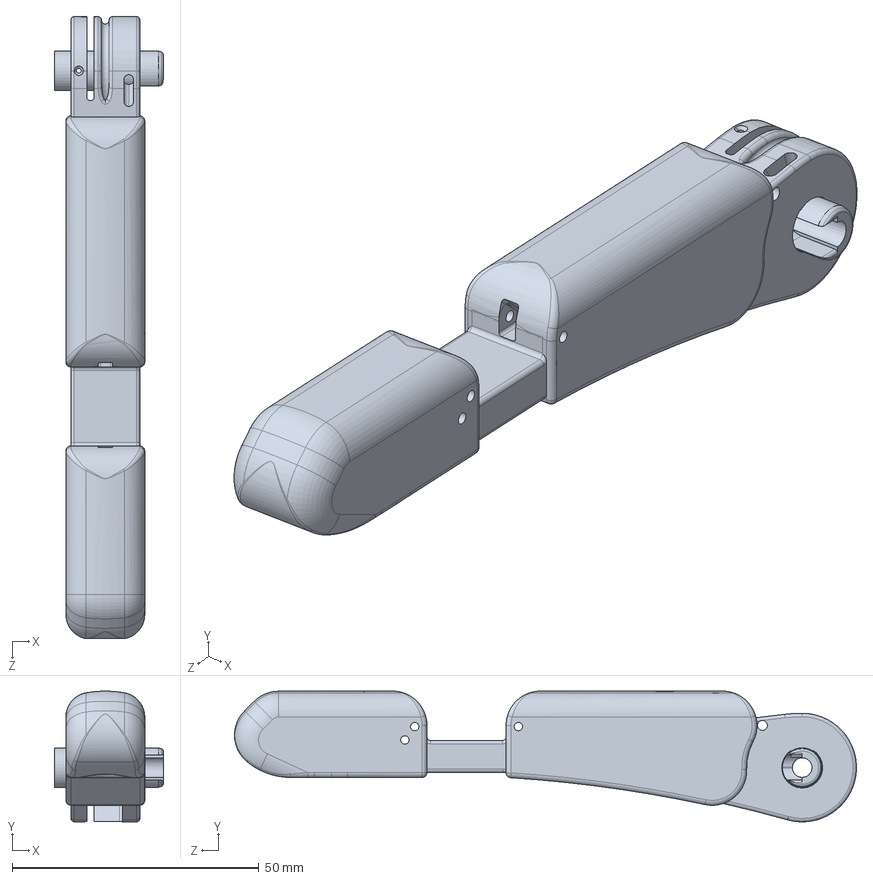
[picture p71: CAD file, 2017-10-08]
B-term/ReflexOne Finger/Finger.SLDPRT
22.0 x 26.5 x 126.0 mm
