nphoang1102/mqp-mech/C-term/Mounting Parts/mounting_house/Camera Mount/Rotate Joint.SLDPRT

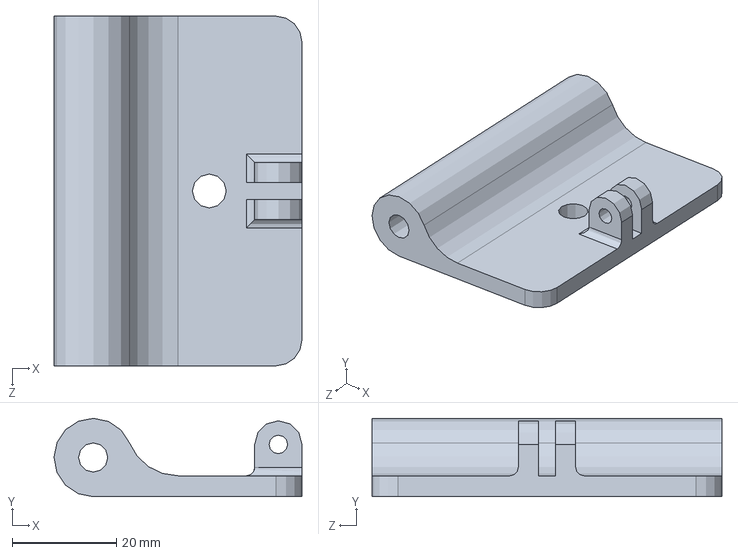
[picture p72: CAD file, 2018-03-26]
C-term/Mounting Parts/mounting_house/Camera Mount/Rotate Joint.SLDPRT
47.5 x 15.0 x 67.0 mm
