nphoang1102/mqp-mech/C-term/PCB Mount/AX-12A connector.SLDPRT

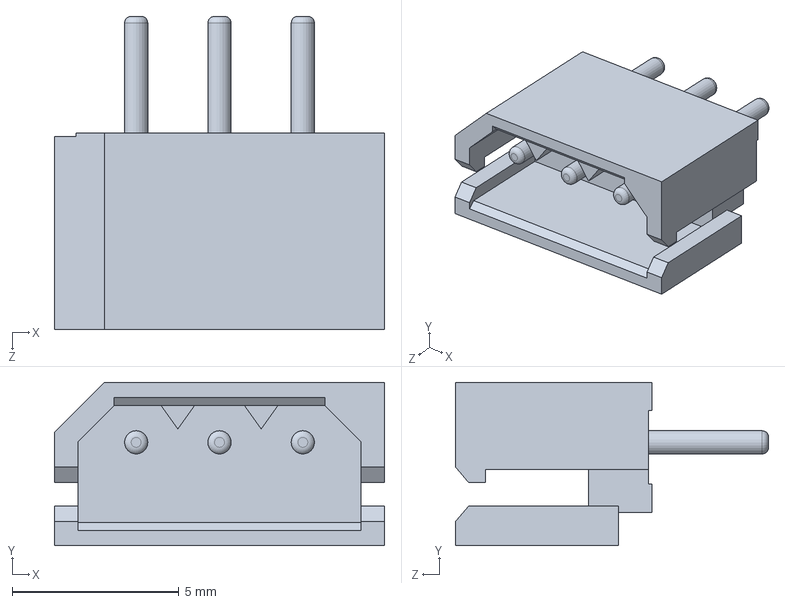
[picture p73: CAD file, 2018-03-26]
C-term/PCB Mount/AX-12A connector.SLDPRT
9.90 x 4.90 x 9.40 mm
