nphoang1102/mqp-mech/B-term/Prototype 1 Fixes (Not Prototype 2 Yet)/two_stage_gear.SLDPRT

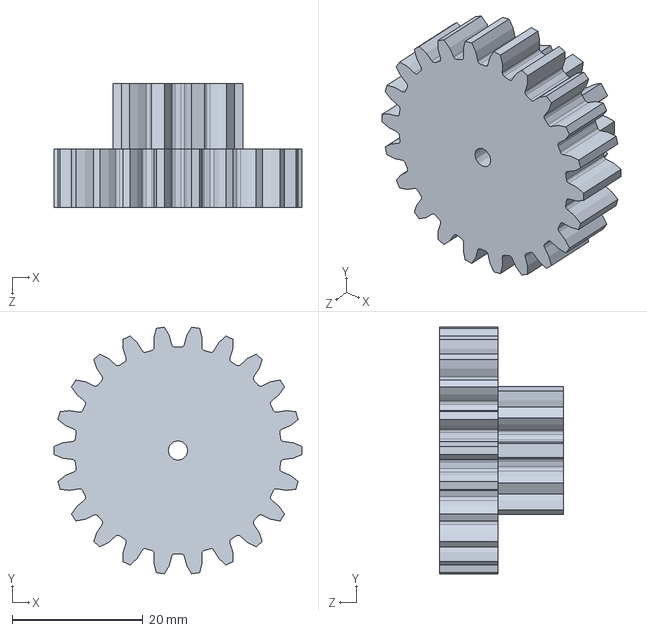
[picture p74: CAD file, 2018-03-26]
B-term/Prototype 1 Fixes (Not Prototype 2 Yet)/two_stage_gear.SLDPRT
38.0 x 37.8 x 19.0 mm
