nphoang1102/mqp-mech/B-term/Prototype 2/gear_drive.SLDPRT

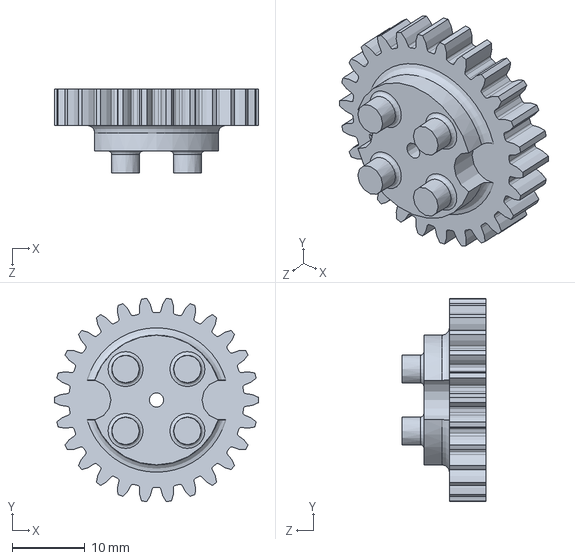
[picture p75: CAD file, 2018-03-26]
B-term/Prototype 2/gear_drive.SLDPRT
28.0 x 27.9 x 11.5 mm
