nphoang1102/mqp-mech/C-term/Mounting Parts/mounting_house/Camera Mount/Wedge.SLDPRT

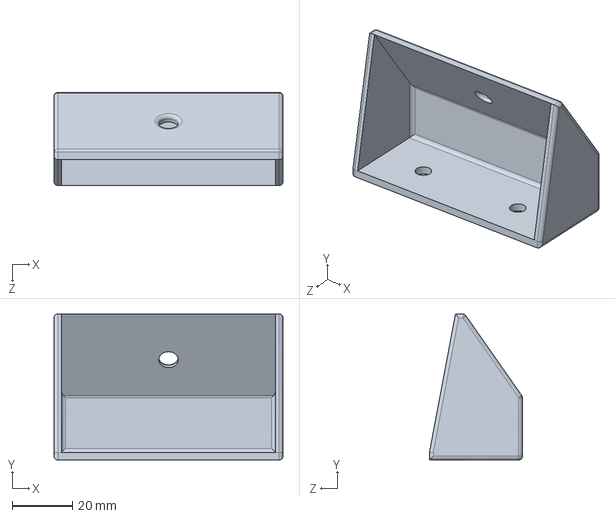
[picture p76: CAD file, 2018-03-26]
C-term/Mounting Parts/mounting_house/Camera Mount/Wedge.SLDPRT
76.2 x 48.5 x 31.0 mm
