nphoang1102/mqp-mech/C-term/Mounting Parts/test_model_housing.SLDPRT

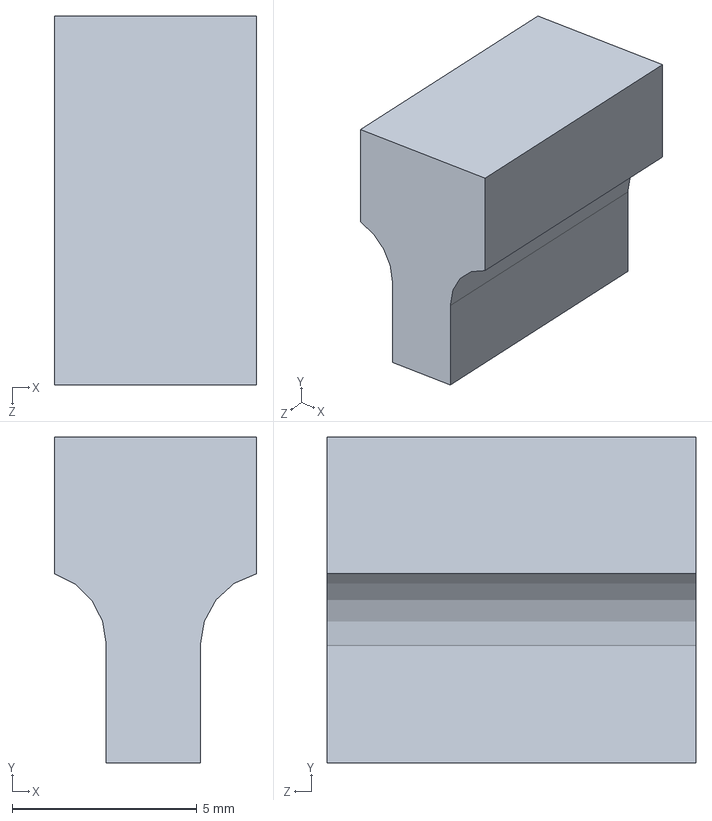
[picture p77: CAD file, 2018-03-26]
C-term/Mounting Parts/test_model_housing.SLDPRT
5.49 x 8.83 x 10.0 mm
