nphoang1102/mqp-mech/C-term/PCB Mount/Pcb board base.SLDPRT

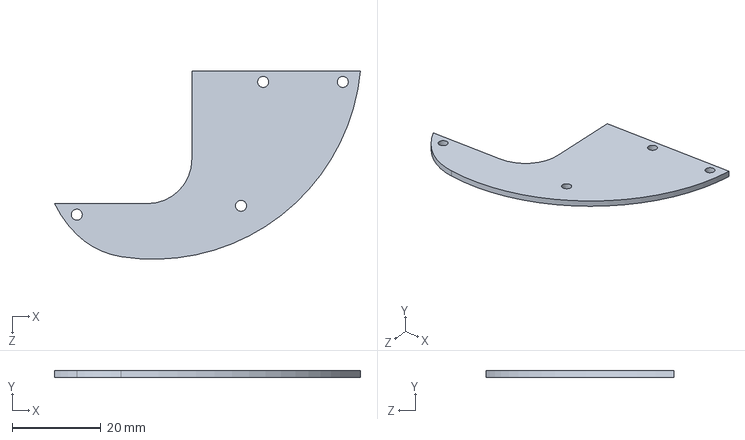
[picture p78: CAD file, 2018-03-26]
C-term/PCB Mount/Pcb board base.SLDPRT
69.2 x 1.50 x 42.6 mm
