nphoang1102/mqp-mech/C-term/STL toPrint/Feb_11_2018/mount_finger_right.STL

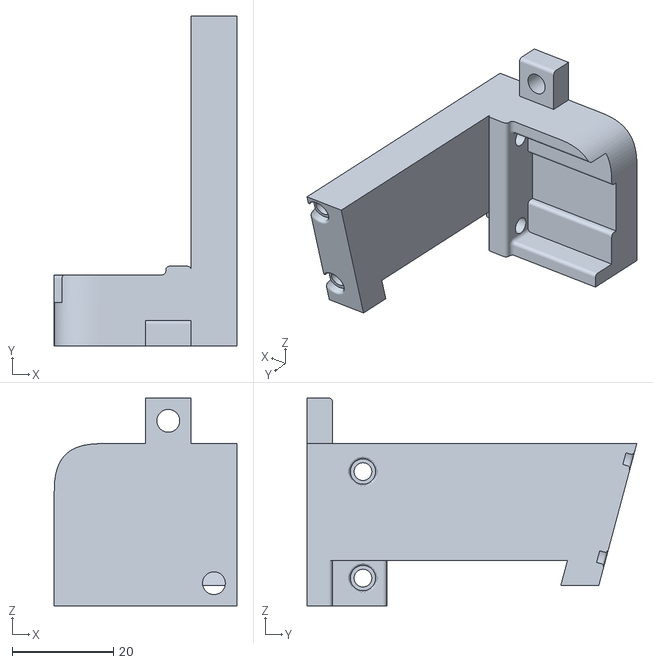
[picture p79: CAD file, 2018-03-26]
C-term/STL toPrint/Feb_11_2018/mount_finger_right.STL
36.0 x 65.0 x 41.0
