nphoang1102/mqp-mech/A-term/drive_gear.SLDPRT

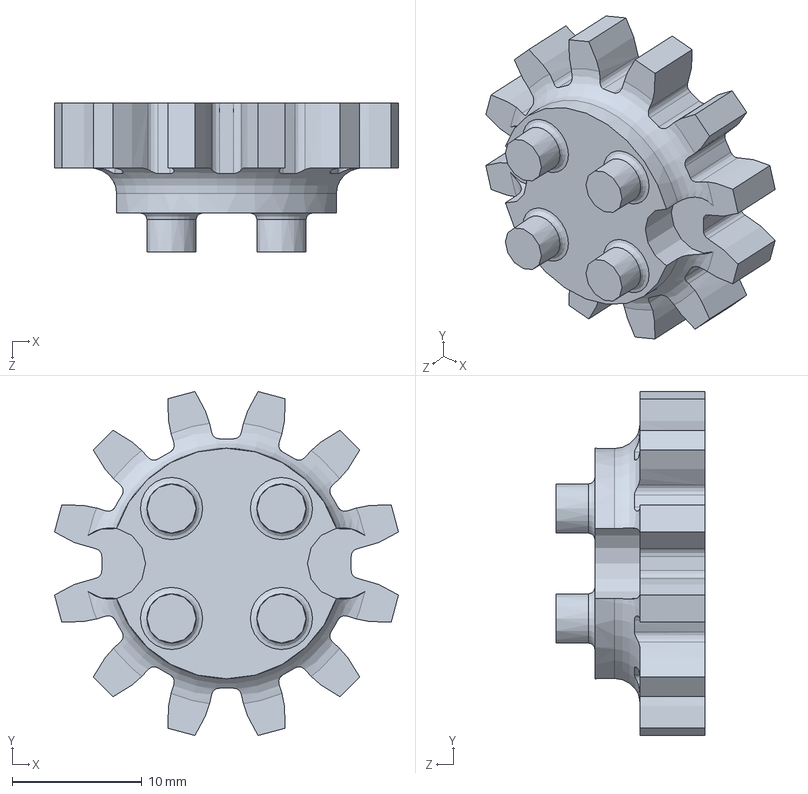
[picture p80: CAD file, 2017-10-22]
A-term/drive_gear.SLDPRT
26.6 x 26.6 x 11.5 mm
