nphoang1102/mqp-mech/C-term/Mounting Parts/DC Fan - 25X25X10.SLDPRT

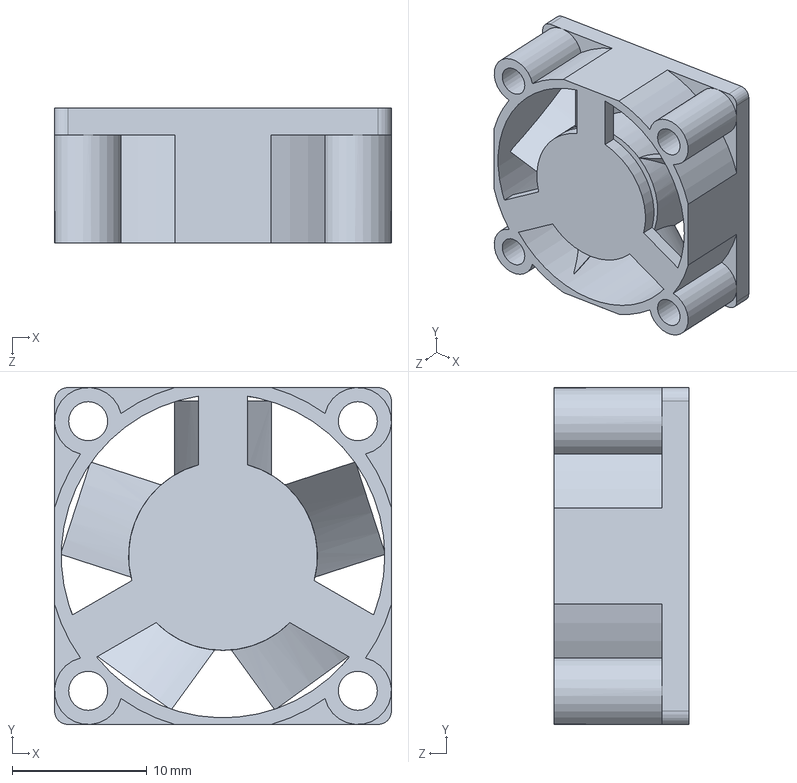
[picture p81: CAD file, 2018-03-26]
C-term/Mounting Parts/DC Fan - 25X25X10.SLDPRT
25.0 x 25.0 x 10.0 mm
