nphoang1102/mqp-mech/C-term/Mounting Parts/mounting_house/Camera Mount/Adjustment plate.SLDPRT

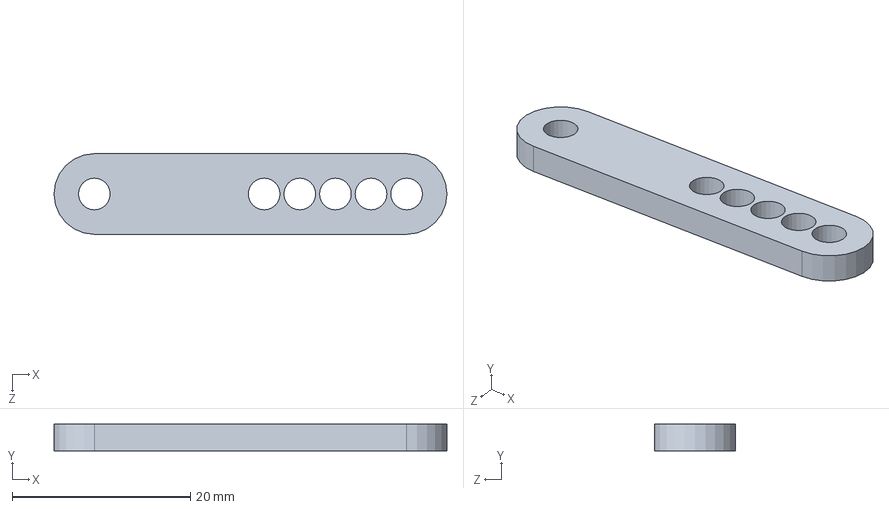
[picture p82: CAD file, 2018-03-26]
C-term/Mounting Parts/mounting_house/Camera Mount/Adjustment plate.SLDPRT
44.1 x 3.00 x 9.06 mm
