nphoang1102/mqp-mech/C-term/PCB Mount/power jack.sldprt

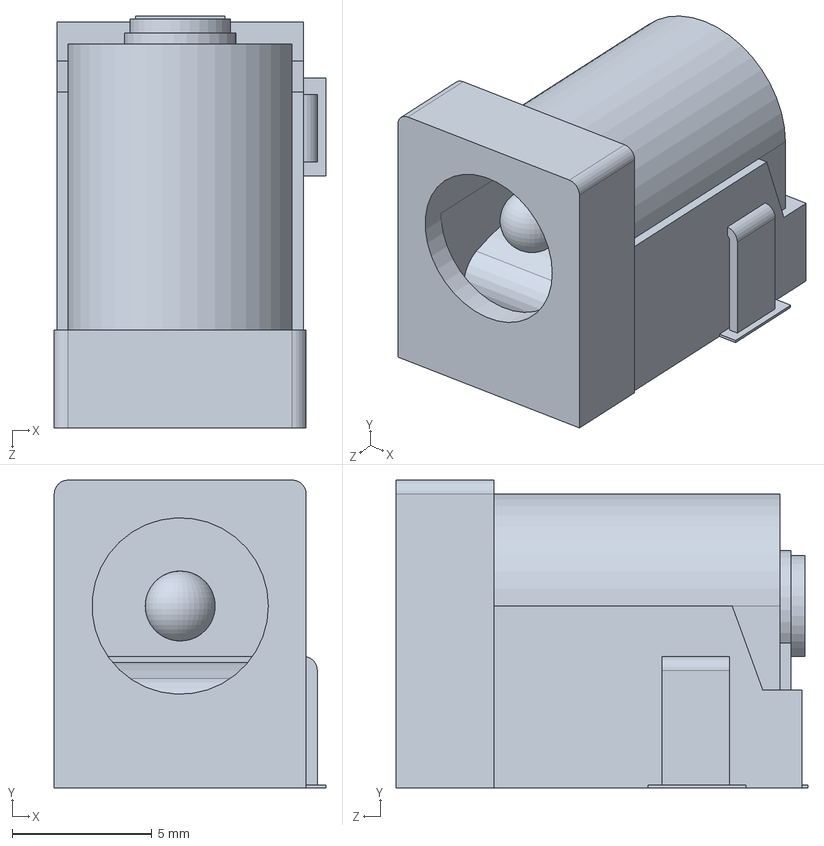
[picture p83: CAD file, 2018-03-26]
C-term/PCB Mount/power jack.sldprt
9.70 x 11.0 x 14.7 mm
