nphoang1102/mqp-mech/A-term/intermediate_gear_top_level.SLDPRT

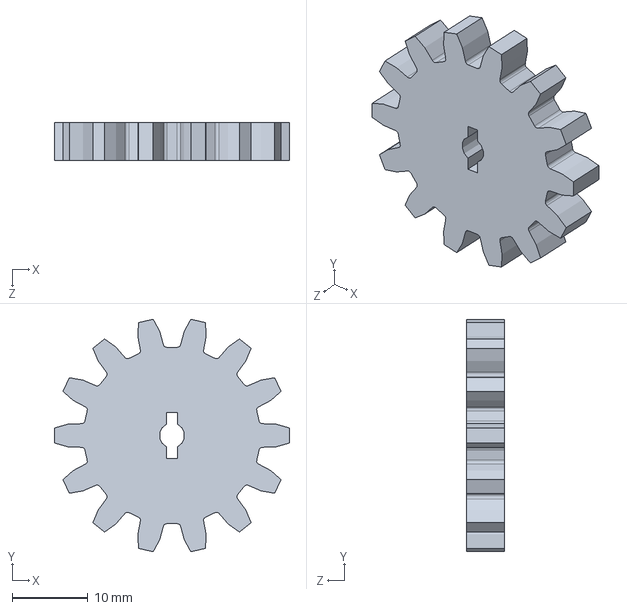
[picture p84: CAD file, 2017-10-22]
A-term/intermediate_gear_top_level.SLDPRT
30.9 x 30.6 x 5.00 mm
