nphoang1102/mqp-mech/B-term/Prototype 2/AX-12A (back off).SLDPRT

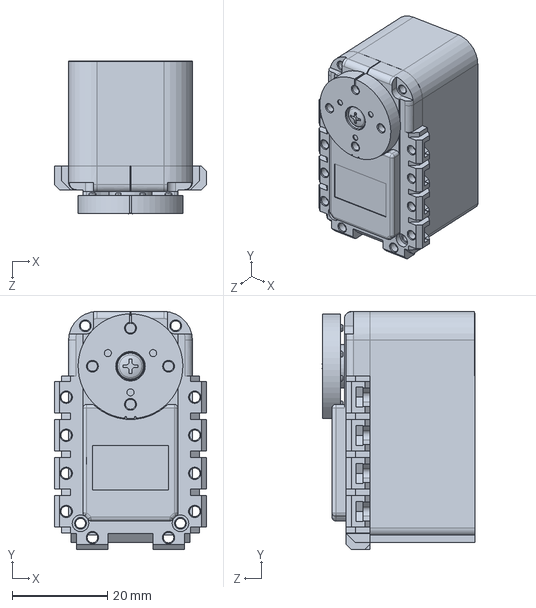
[picture p85: CAD file, 2018-03-26]
B-term/Prototype 2/AX-12A (back off).SLDPRT
32.0 x 50.0 x 32.0 mm
