nphoang1102/mqp-mech/C-term/Mounting Parts/mounting_house/Camera Mount/Camera Adapter Base.SLDPRT

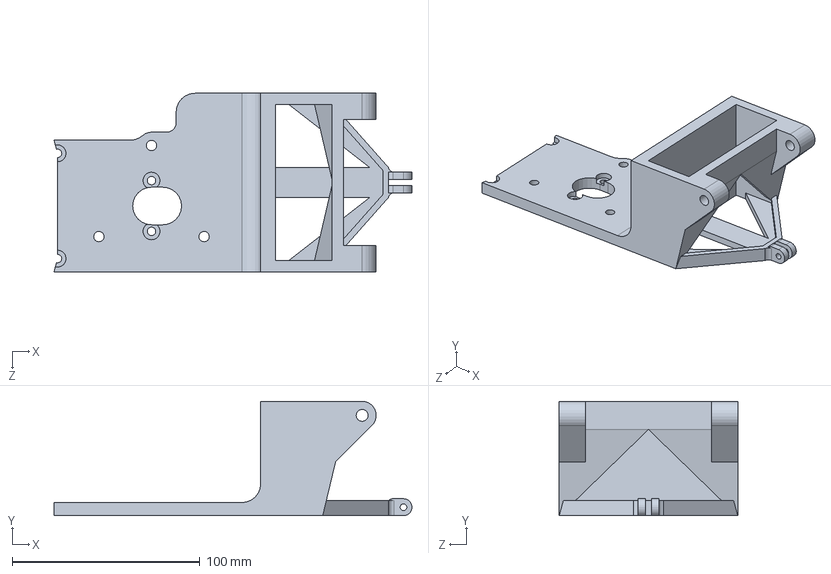
[picture p86: CAD file, 2018-03-26]
C-term/Mounting Parts/mounting_house/Camera Mount/Camera Adapter Base.SLDPRT
190.5 x 60.9 x 95.0 mm
