nphoang1102/mqp-mech/A-term/intermediate_gear_bottom_level.SLDPRT

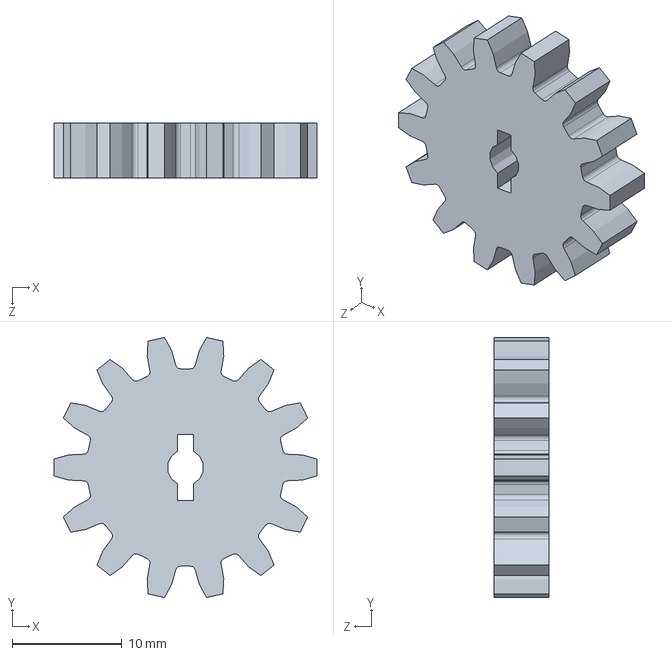
[picture p87: CAD file, 2017-10-22]
A-term/intermediate_gear_bottom_level.SLDPRT
24.0 x 23.7 x 5.00 mm
