nphoang1102/mqp-mech/B-term/Prototype 1 Fixes (Not Prototype 2 Yet)/AX12_thumb_mount.SLDPRT

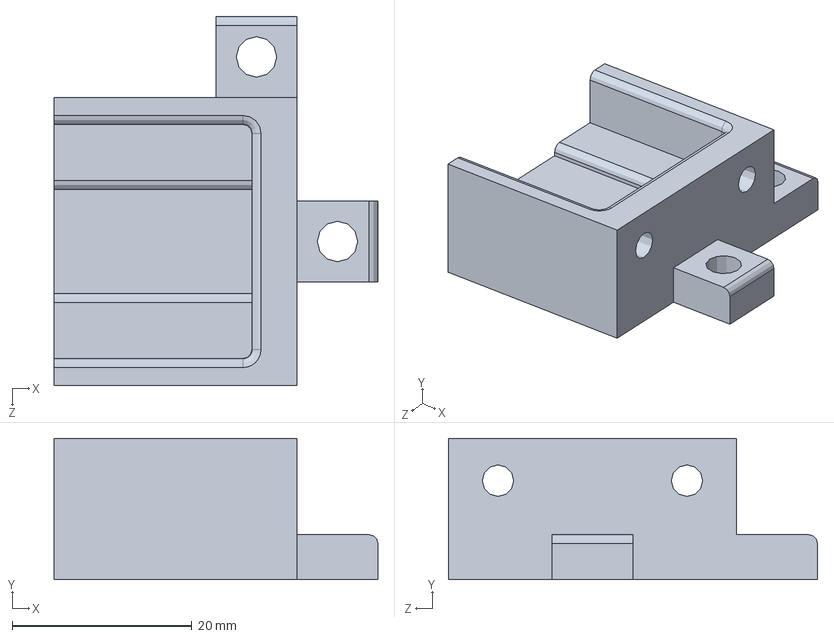
[picture p88: CAD file, 2018-03-26]
B-term/Prototype 1 Fixes (Not Prototype 2 Yet)/AX12_thumb_mount.SLDPRT
36.0 x 15.7 x 41.0 mm
