nphoang1102/mqp-mech/A-term/finger_gear.SLDPRT

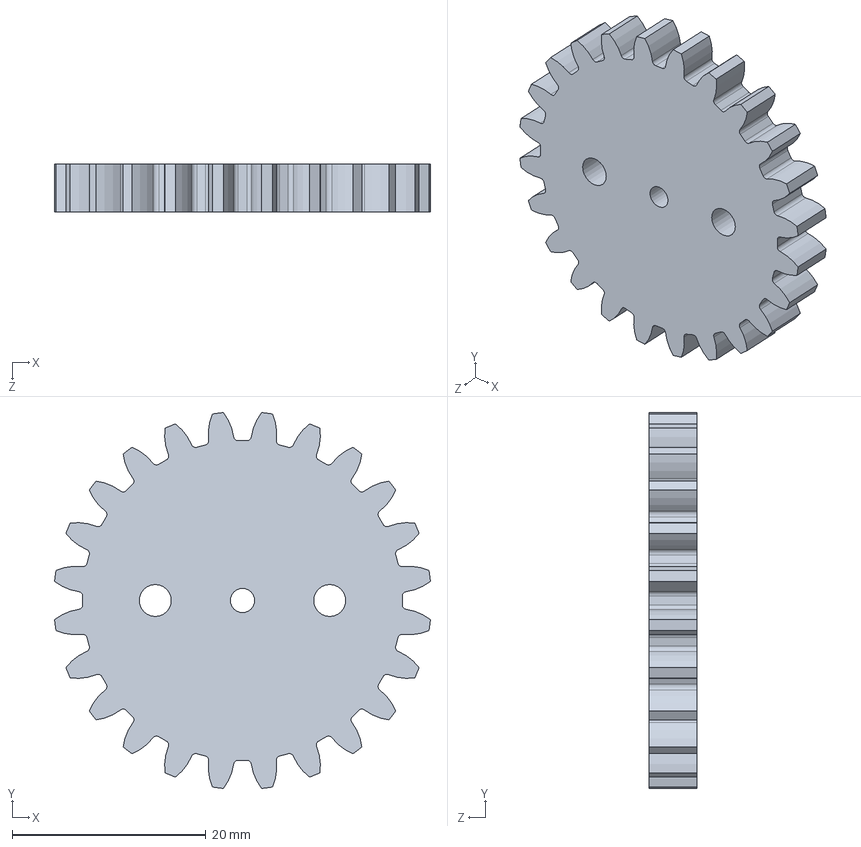
[picture p89: CAD file, 2017-10-22]
A-term/finger_gear.SLDPRT
38.8 x 38.8 x 5.00 mm
