nphoang1102/mqp-mech/B-term/Prototype 1 Fixes (Not Prototype 2 Yet)/knuckle_mount_test_modified.SLDPRT

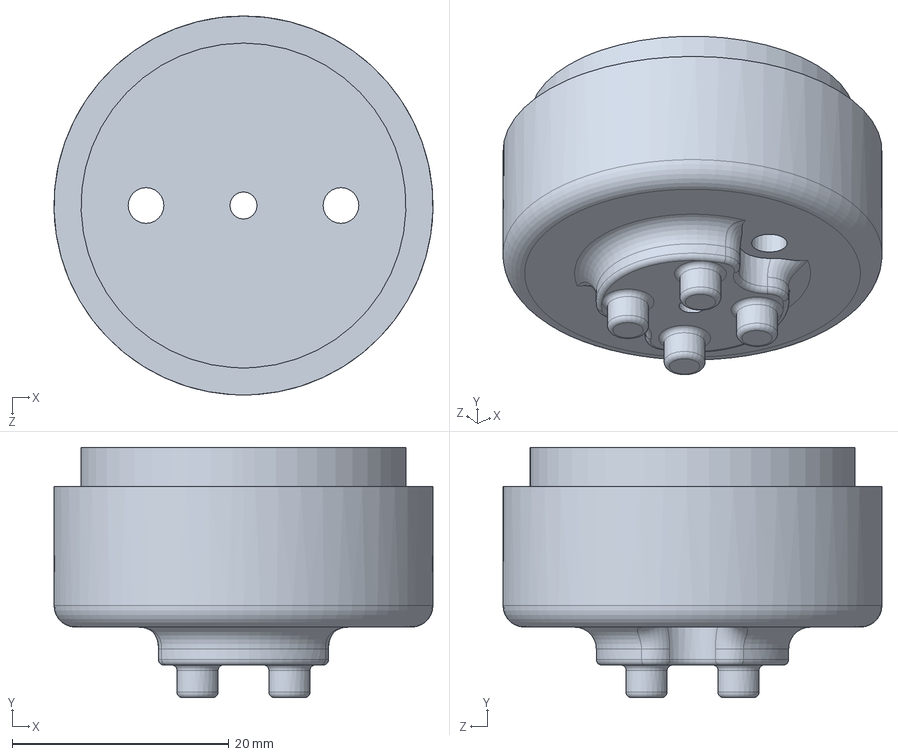
[picture p90: CAD file, 2018-03-26]
B-term/Prototype 1 Fixes (Not Prototype 2 Yet)/knuckle_mount_test_modified.SLDPRT
35.0 x 23.1 x 35.0 mm
