nphoang1102/mqp-mech/B-term/Prototype 2/XL320.SLDPRT

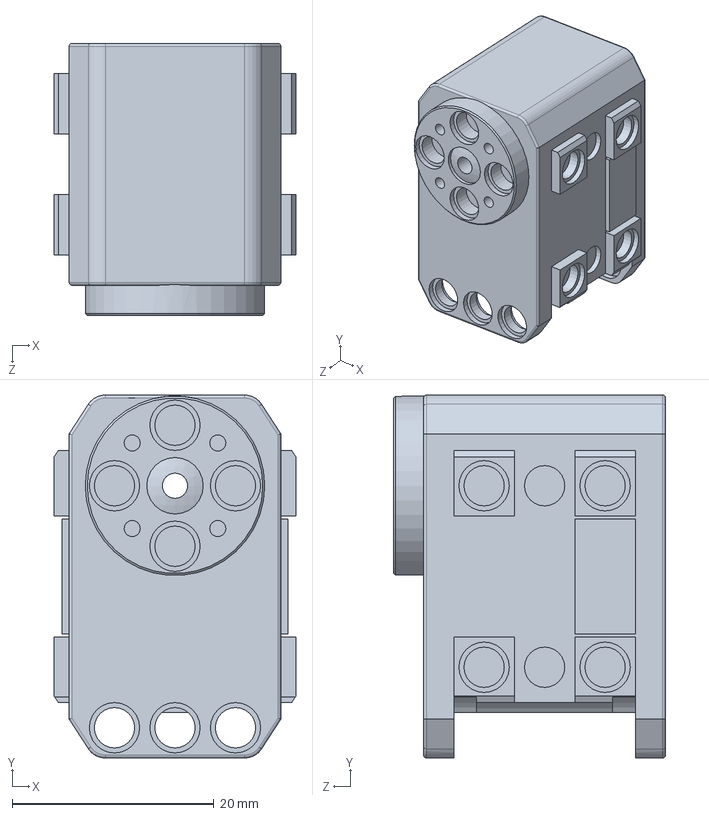
[picture p91: CAD file, 2018-03-26]
B-term/Prototype 2/XL320.SLDPRT
24.0 x 36.0 x 27.0 mm
