nphoang1102/mqp-mech/A-term/AX12_front_mount_right.SLDPRT

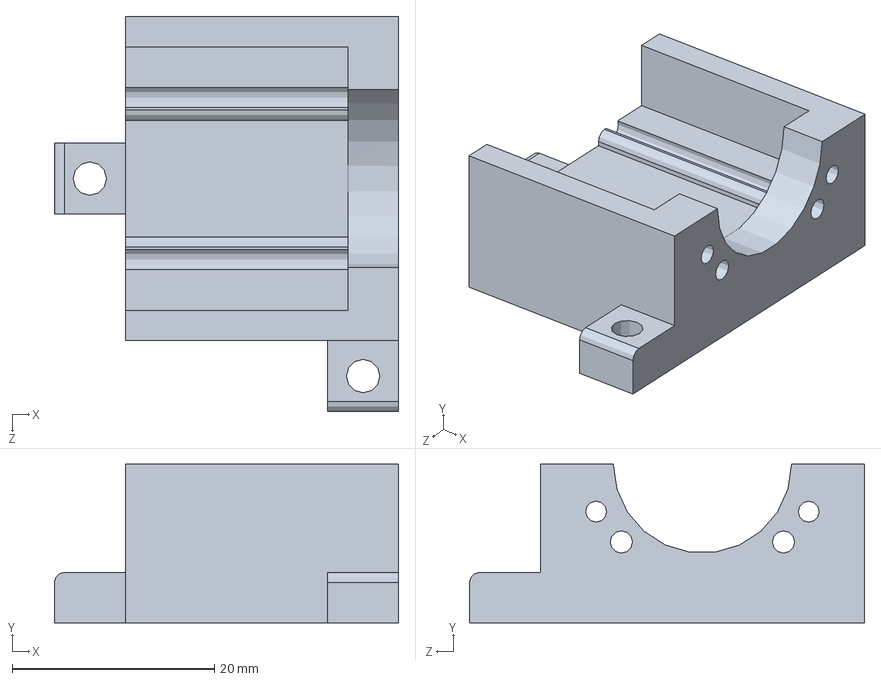
[picture p92: CAD file, 2017-10-21]
A-term/AX12_front_mount_right.SLDPRT
34.0 x 15.7 x 39.0 mm
