nphoang1102/mqp-mech/B-term/Prototype 1 Fixes (Not Prototype 2 Yet)/AX12_fingers_mount.SLDPRT

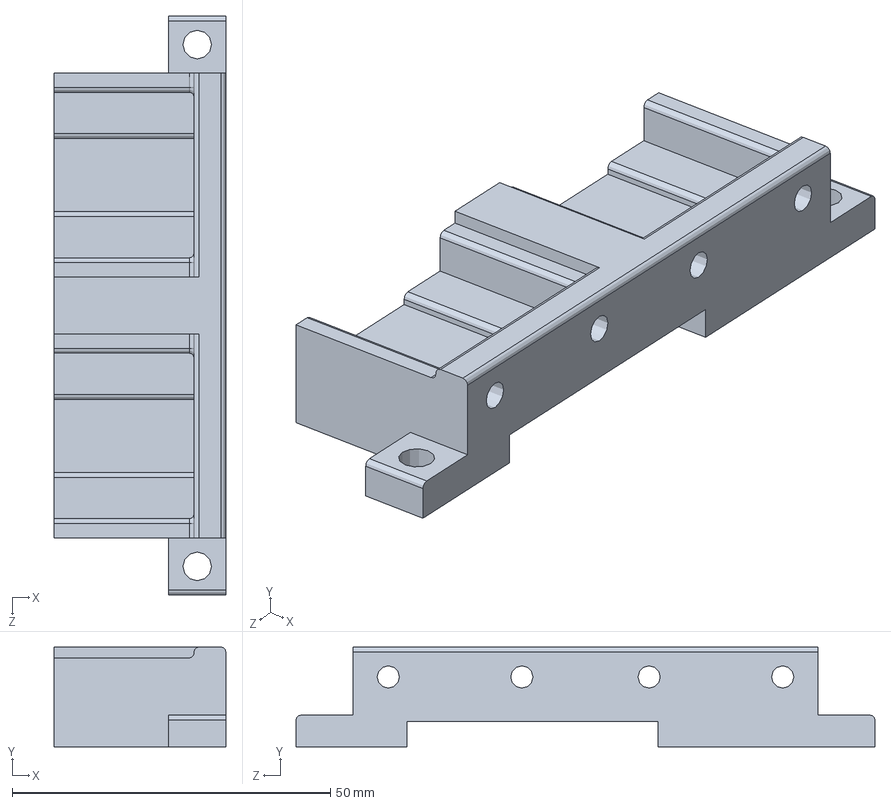
[picture p93: CAD file, 2018-03-26]
B-term/Prototype 1 Fixes (Not Prototype 2 Yet)/AX12_fingers_mount.SLDPRT
27.0 x 15.7 x 91.0 mm
