nphoang1102/mqp-mech/C-term/STL toPrint/Feb_28_2018_RapidPrototyping/gear_drive.STL

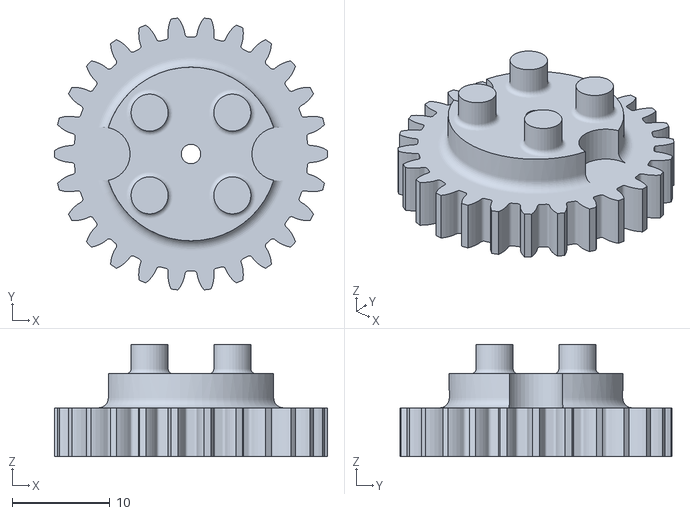
[picture p94: CAD file, 2018-03-26]
C-term/STL toPrint/Feb_28_2018_RapidPrototyping/gear_drive.STL
28.0 x 27.9 x 11.5
