nphoang1102/mqp-mech/A-term/knuckle_mount_test_modified.SLDPRT

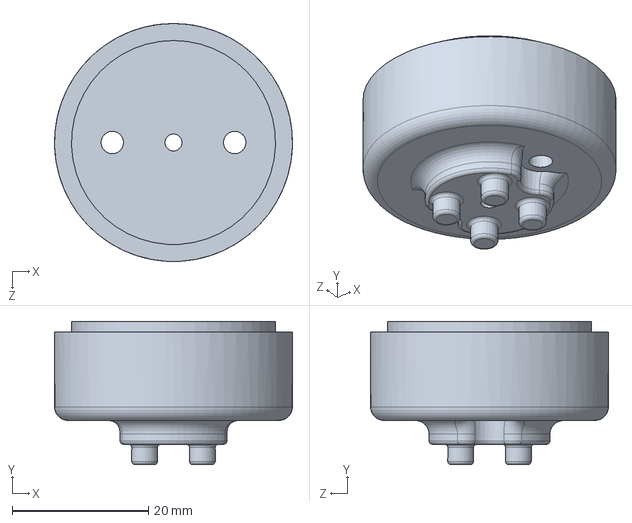
[picture p95: CAD file, 2017-10-21]
A-term/knuckle_mount_test_modified.SLDPRT
35.0 x 21.1 x 35.0 mm
