nphoang1102/mqp-mech/C-term/STL toPrint/Feb_28_2018_RapidPrototyping/mount_knuckle_test_modified.STL

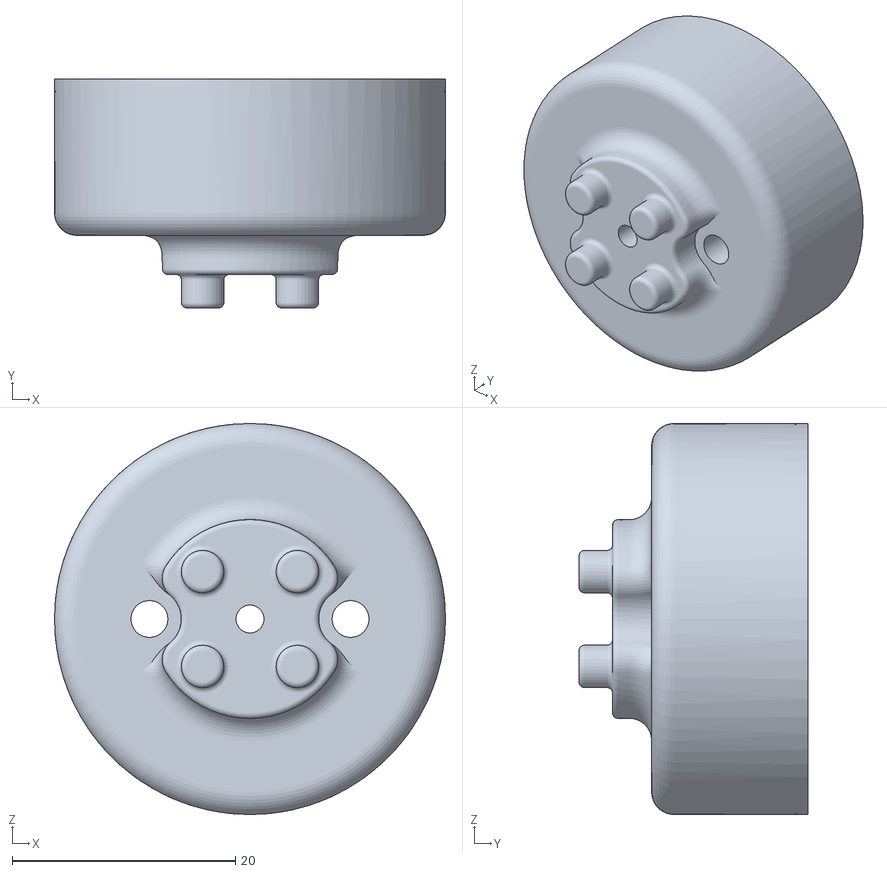
[picture p96: CAD file, 2018-03-26]
C-term/STL toPrint/Feb_28_2018_RapidPrototyping/mount_knuckle_test_modified.STL
35.0 x 20.5 x 35.0
