nphoang1102/mqp-mech/B-term/Prototype 1 Fixes (Not Prototype 2 Yet)/base_prototype_test.SLDPRT

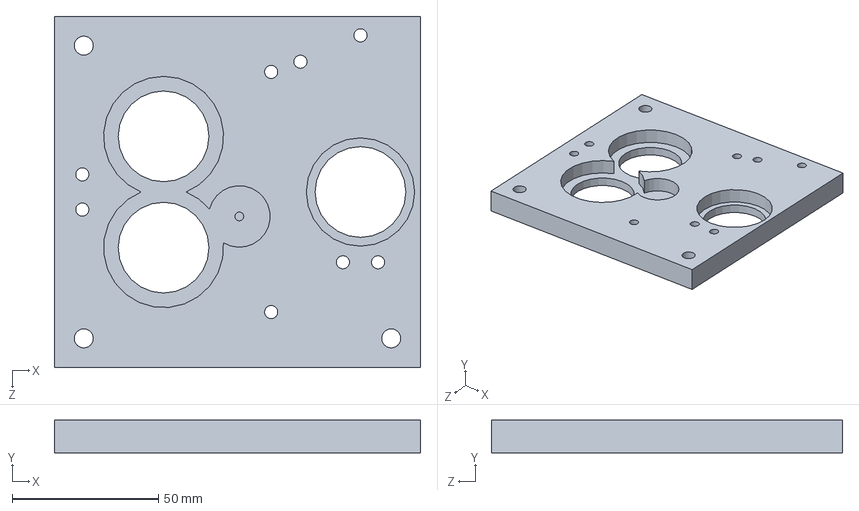
[picture p97: CAD file, 2018-03-26]
B-term/Prototype 1 Fixes (Not Prototype 2 Yet)/base_prototype_test.SLDPRT
125.0 x 11.2 x 120.0 mm
