nphoang1102/mqp-mech/B-term/Prototype 1 Fixes (Not Prototype 2 Yet)/top_part_base_prototype.SLDPRT

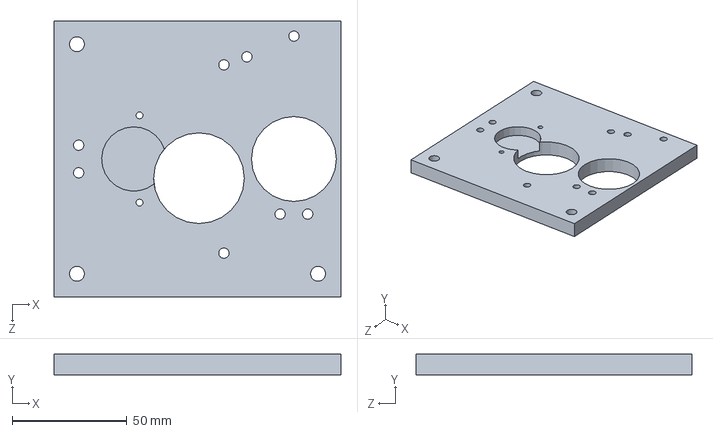
[picture p98: CAD file, 2018-03-26]
B-term/Prototype 1 Fixes (Not Prototype 2 Yet)/top_part_base_prototype.SLDPRT
125.0 x 9.00 x 120.0 mm
