nphoang1102/mqp-mech/B-term/Prototype 1 Fixes (Not Prototype 2 Yet)/XL320_thumb_mount.SLDPRT

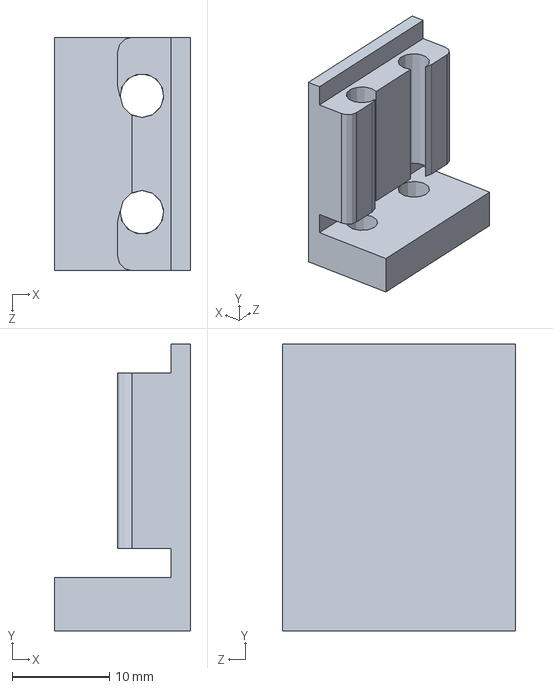
[picture p99: CAD file, 2018-03-26]
B-term/Prototype 1 Fixes (Not Prototype 2 Yet)/XL320_thumb_mount.SLDPRT
14.0 x 29.5 x 24.0 mm
