nphoang1102/mqp-mech/B-term/Prototype 2/mount_finger_right.SLDPRT

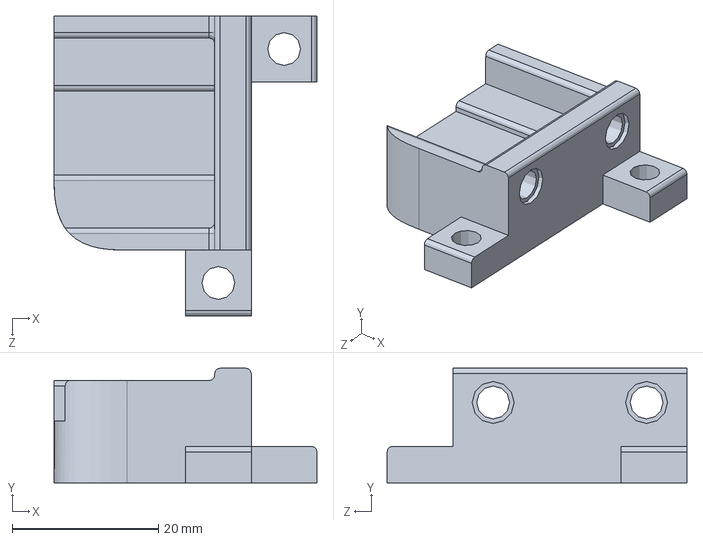
[picture p100: CAD file, 2018-03-26]
B-term/Prototype 2/mount_finger_right.SLDPRT
36.0 x 15.7 x 41.0 mm
